5Breeze/WKnob/APP/BTHome/mbedtls/include/mbedtls/ssl.h

/**
 * \file ssl.h
 *
 * \brief SSL/TLS functions.
 */
/*
 *  Copyright The Mbed TLS Contributors
 *  SPDX-License-Identifier: Apache-2.0
 *
 *  Licensed under the Apache License, Version 2.0 (the "License"); you may
 *  not use this file except in compliance with the License.
 *  You may obtain a copy of the License at
 *
 *  http://www.apache.org/licenses/LICENSE-2.0
 *
 *  Unless required by applicable law or agreed to in writing, software
 *  distributed under the License is distributed on an "AS IS" BASIS, WITHOUT
 *  WARRANTIES OR CONDITIONS OF ANY KIND, either express or implied.
 *  See the License for the specific language governing permissions and
 *  limitations under the License.
 */
#ifndef MBEDTLS_SSL_H
#define MBEDTLS_SSL_H

#if !defined(MBEDTLS_CONFIG_FILE)
#include "config.h"
#else
#include MBEDTLS_CONFIG_FILE
#endif

#include "bignum.h"
#include "ecp.h"

#include "ssl_ciphersuites.h"

#if defined(MBEDTLS_X509_CRT_PARSE_C)
#include "x509_crt.h"
#include "x509_crl.h"
#endif

#if defined(MBEDTLS_DHM_C)
#include "dhm.h"
#endif

#if defined(MBEDTLS_ECDH_C)
#include "ecdh.h"
#endif

#if defined(MBEDTLS_ZLIB_SUPPORT)

#if defined(MBEDTLS_DEPRECATED_WARNING)
#warning "Record compression support via MBEDTLS_ZLIB_SUPPORT is deprecated and will be removed in the next major revision of the library"
#endif

#if defined(MBEDTLS_DEPRECATED_REMOVED)
#error "Record compression support via MBEDTLS_ZLIB_SUPPORT is deprecated and cannot be used if MBEDTLS_DEPRECATED_REMOVED is set"
#endif

#include "zlib.h"
#endif

#if defined(MBEDTLS_HAVE_TIME)
#include "platform_time.h"
#endif

#if defined(MBEDTLS_USE_PSA_CRYPTO)
#include "psa/crypto.h"
#endif /* MBEDTLS_USE_PSA_CRYPTO */

/*
 * SSL Error codes
 */
#define MBEDTLS_ERR_SSL_FEATURE_UNAVAILABLE               -0x7080  /**< The requested feature is not available. */
#define MBEDTLS_ERR_SSL_BAD_INPUT_DATA                    -0x7100  /**< Bad input parameters to function. */
#define MBEDTLS_ERR_SSL_INVALID_MAC                       -0x7180  /**< Verification of the message MAC failed. */
#define MBEDTLS_ERR_SSL_INVALID_RECORD                    -0x7200  /**< An invalid SSL record was received. */
#define MBEDTLS_ERR_SSL_CONN_EOF                          -0x7280  /**< The connection indicated an EOF. */
#define MBEDTLS_ERR_SSL_UNKNOWN_CIPHER                    -0x7300  /**< An unknown cipher was received. */
#define MBEDTLS_ERR_SSL_NO_CIPHER_CHOSEN                  -0x7380  /**< The server has no ciphersuites in common with the client. */
#define MBEDTLS_ERR_SSL_NO_RNG                            -0x7400  /**< No RNG was provided to the SSL module. */
#define MBEDTLS_ERR_SSL_NO_CLIENT_CERTIFICATE             -0x7480  /**< No client certification received from the client, but required by the authentication mode. */
#define MBEDTLS_ERR_SSL_CERTIFICATE_TOO_LARGE             -0x7500  /**< Our own certificate(s) is/are too large to send in an SSL message. */
#define MBEDTLS_ERR_SSL_CERTIFICATE_REQUIRED              -0x7580  /**< The own certificate is not set, but needed by the server. */
#define MBEDTLS_ERR_SSL_PRIVATE_KEY_REQUIRED              -0x7600  /**< The own private key or pre-shared key is not set, but needed. */
#define MBEDTLS_ERR_SSL_CA_CHAIN_REQUIRED                 -0x7680  /**< No CA Chain is set, but required to operate. */
#define MBEDTLS_ERR_SSL_UNEXPECTED_MESSAGE                -0x7700  /**< An unexpected message was received from our peer. */
#define MBEDTLS_ERR_SSL_FATAL_ALERT_MESSAGE               -0x7780  /**< A fatal alert message was received from our peer. */
#define MBEDTLS_ERR_SSL_PEER_VERIFY_FAILED                -0x7800  /**< Verification of our peer failed. */
#define MBEDTLS_ERR_SSL_PEER_CLOSE_NOTIFY                 -0x7880  /**< The peer notified us that the connection is going to be closed. */
#define MBEDTLS_ERR_SSL_BAD_HS_CLIENT_HELLO               -0x7900  /**< Processing of the ClientHello handshake message failed. */
#define MBEDTLS_ERR_SSL_BAD_HS_SERVER_HELLO               -0x7980  /**< Processing of the ServerHello handshake message failed. */
#define MBEDTLS_ERR_SSL_BAD_HS_CERTIFICATE                -0x7A00  /**< Processing of the Certificate handshake message failed. */
#define MBEDTLS_ERR_SSL_BAD_HS_CERTIFICATE_REQUEST        -0x7A80  /**< Processing of the CertificateRequest handshake message failed. */
#define MBEDTLS_ERR_SSL_BAD_HS_SERVER_KEY_EXCHANGE        -0x7B00  /**< Processing of the ServerKeyExchange handshake message failed. */
#define MBEDTLS_ERR_SSL_BAD_HS_SERVER_HELLO_DONE          -0x7B80  /**< Processing of the ServerHelloDone handshake message failed. */
#define MBEDTLS_ERR_SSL_BAD_HS_CLIENT_KEY_EXCHANGE        -0x7C00  /**< Processing of the ClientKeyExchange handshake message failed. */
#define MBEDTLS_ERR_SSL_BAD_HS_CLIENT_KEY_EXCHANGE_RP     -0x7C80  /**< Processing of the ClientKeyExchange handshake message failed in DHM / ECDH Read Public. */
#define MBEDTLS_ERR_SSL_BAD_HS_CLIENT_KEY_EXCHANGE_CS     -0x7D00  /**< Processing of the ClientKeyExchange handshake message failed in DHM / ECDH Calculate Secret. */
#define MBEDTLS_ERR_SSL_BAD_HS_CERTIFICATE_VERIFY         -0x7D80  /**< Processing of the CertificateVerify handshake message failed. */
#define MBEDTLS_ERR_SSL_BAD_HS_CHANGE_CIPHER_SPEC         -0x7E00  /**< Processing of the ChangeCipherSpec handshake message failed. */
#define MBEDTLS_ERR_SSL_BAD_HS_FINISHED                   -0x7E80  /**< Processing of the Finished handshake message failed. */
#define MBEDTLS_ERR_SSL_ALLOC_FAILED                      -0x7F00  /**< Memory allocation failed */
#define MBEDTLS_ERR_SSL_HW_ACCEL_FAILED                   -0x7F80  /**< Hardware acceleration function returned with error */
#define MBEDTLS_ERR_SSL_HW_ACCEL_FALLTHROUGH              -0x6F80  /**< Hardware acceleration function skipped / left alone data */
#define MBEDTLS_ERR_SSL_COMPRESSION_FAILED                -0x6F00  /**< Processing of the compression / decompression failed */
#define MBEDTLS_ERR_SSL_BAD_HS_PROTOCOL_VERSION           -0x6E80  /**< Handshake protocol not within min/max boundaries */
#define MBEDTLS_ERR_SSL_BAD_HS_NEW_SESSION_TICKET         -0x6E00  /**< Processing of the NewSessionTicket handshake message failed. */
#define MBEDTLS_ERR_SSL_SESSION_TICKET_EXPIRED            -0x6D80  /**< Session ticket has expired. */
#define MBEDTLS_ERR_SSL_PK_TYPE_MISMATCH                  -0x6D00  /**< Public key type mismatch (eg, asked for RSA key exchange and presented EC key) */
#define MBEDTLS_ERR_SSL_UNKNOWN_IDENTITY                  -0x6C80  /**< Unknown identity received (eg, PSK identity) */
#define MBEDTLS_ERR_SSL_INTERNAL_ERROR                    -0x6C00  /**< Internal error (eg, unexpected failure in lower-level module) */
#define MBEDTLS_ERR_SSL_COUNTER_WRAPPING                  -0x6B80  /**< A counter would wrap (eg, too many messages exchanged). */
#define MBEDTLS_ERR_SSL_WAITING_SERVER_HELLO_RENEGO       -0x6B00  /**< Unexpected message at ServerHello in renegotiation. */
#define MBEDTLS_ERR_SSL_HELLO_VERIFY_REQUIRED             -0x6A80  /**< DTLS client must retry for hello verification */
#define MBEDTLS_ERR_SSL_BUFFER_TOO_SMALL                  -0x6A00  /**< A buffer is too small to receive or write a message */
#define MBEDTLS_ERR_SSL_NO_USABLE_CIPHERSUITE             -0x6980  /**< None of the common ciphersuites is usable (eg, no suitable certificate, see debug messages). */
#define MBEDTLS_ERR_SSL_WANT_READ                         -0x6900  /**< No data of requested type currently available on underlying transport. */
#define MBEDTLS_ERR_SSL_WANT_WRITE                        -0x6880  /**< Connection requires a write call. */
#define MBEDTLS_ERR_SSL_TIMEOUT                           -0x6800  /**< The operation timed out. */
#define MBEDTLS_ERR_SSL_CLIENT_RECONNECT                  -0x6780  /**< The client initiated a reconnect from the same port. */
#define MBEDTLS_ERR_SSL_UNEXPECTED_RECORD                 -0x6700  /**< Record header looks valid but is not expected. */
#define MBEDTLS_ERR_SSL_NON_FATAL                         -0x6680  /**< The alert message received indicates a non-fatal error. */
#define MBEDTLS_ERR_SSL_INVALID_VERIFY_HASH               -0x6600  /**< Couldn't set the hash for verifying CertificateVerify */
#define MBEDTLS_ERR_SSL_CONTINUE_PROCESSING               -0x6580  /**< Internal-only message signaling that further message-processing should be done */
#define MBEDTLS_ERR_SSL_ASYNC_IN_PROGRESS                 -0x6500  /**< The asynchronous operation is not completed yet. */
#define MBEDTLS_ERR_SSL_EARLY_MESSAGE                     -0x6480  /**< Internal-only message signaling that a message arrived early. */
#define MBEDTLS_ERR_SSL_UNEXPECTED_CID                    -0x6000  /**< An encrypted DTLS-frame with an unexpected CID was received. */
#define MBEDTLS_ERR_SSL_VERSION_MISMATCH                  -0x5F00  /**< An operation failed due to an unexpected version or configuration. */
#define MBEDTLS_ERR_SSL_CRYPTO_IN_PROGRESS                -0x7000  /**< A cryptographic operation is in progress. Try again later. */
#define MBEDTLS_ERR_SSL_BAD_CONFIG                        -0x5E80  /**< Invalid value in SSL config */

/*
 * Various constants
 */
#define MBEDTLS_SSL_MAJOR_VERSION_3             3
#define MBEDTLS_SSL_MINOR_VERSION_0             0   /*!< SSL v3.0 */
#define MBEDTLS_SSL_MINOR_VERSION_1             1   /*!< TLS v1.0 */
#define MBEDTLS_SSL_MINOR_VERSION_2             2   /*!< TLS v1.1 */
#define MBEDTLS_SSL_MINOR_VERSION_3             3   /*!< TLS v1.2 */
#define MBEDTLS_SSL_MINOR_VERSION_4             4   /*!< TLS v1.3 (experimental) */

#define MBEDTLS_SSL_TRANSPORT_STREAM            0   /*!< TLS      */
#define MBEDTLS_SSL_TRANSPORT_DATAGRAM          1   /*!< DTLS     */

#define MBEDTLS_SSL_MAX_HOST_NAME_LEN           255 /*!< Maximum host name defined in RFC 1035 */
#define MBEDTLS_SSL_MAX_ALPN_NAME_LEN           255 /*!< Maximum size in bytes of a protocol name in alpn ext., RFC 7301 */

#define MBEDTLS_SSL_MAX_ALPN_LIST_LEN           65535 /*!< Maximum size in bytes of list in alpn ext., RFC 7301          */

/* RFC 6066 section 4, see also mfl_code_to_length in ssl_tls.c
 * NONE must be zero so that memset()ing structure to zero works */
#define MBEDTLS_SSL_MAX_FRAG_LEN_NONE           0   /*!< don't use this extension   */
#define MBEDTLS_SSL_MAX_FRAG_LEN_512            1   /*!< MaxFragmentLength 2^9      */
#define MBEDTLS_SSL_MAX_FRAG_LEN_1024           2   /*!< MaxFragmentLength 2^10     */
#define MBEDTLS_SSL_MAX_FRAG_LEN_2048           3   /*!< MaxFragmentLength 2^11     */
#define MBEDTLS_SSL_MAX_FRAG_LEN_4096           4   /*!< MaxFragmentLength 2^12     */
#define MBEDTLS_SSL_MAX_FRAG_LEN_INVALID        5   /*!< first invalid value        */

#define MBEDTLS_SSL_IS_CLIENT                   0
#define MBEDTLS_SSL_IS_SERVER                   1

#define MBEDTLS_SSL_IS_NOT_FALLBACK             0
#define MBEDTLS_SSL_IS_FALLBACK                 1

#define MBEDTLS_SSL_EXTENDED_MS_DISABLED        0
#define MBEDTLS_SSL_EXTENDED_MS_ENABLED         1

#define MBEDTLS_SSL_CID_DISABLED                0
#define MBEDTLS_SSL_CID_ENABLED                 1

#define MBEDTLS_SSL_ETM_DISABLED                0
#define MBEDTLS_SSL_ETM_ENABLED                 1

#define MBEDTLS_SSL_COMPRESS_NULL               0
#define MBEDTLS_SSL_COMPRESS_DEFLATE            1

#define MBEDTLS_SSL_VERIFY_NONE                 0
#define MBEDTLS_SSL_VERIFY_OPTIONAL             1
#define MBEDTLS_SSL_VERIFY_REQUIRED             2
#define MBEDTLS_SSL_VERIFY_UNSET                3 /* Used only for sni_authmode */

#define MBEDTLS_SSL_LEGACY_RENEGOTIATION        0
#define MBEDTLS_SSL_SECURE_RENEGOTIATION        1

#define MBEDTLS_SSL_RENEGOTIATION_DISABLED      0
#define MBEDTLS_SSL_RENEGOTIATION_ENABLED       1

#define MBEDTLS_SSL_ANTI_REPLAY_DISABLED        0
#define MBEDTLS_SSL_ANTI_REPLAY_ENABLED         1

#define MBEDTLS_SSL_RENEGOTIATION_NOT_ENFORCED  -1
#define MBEDTLS_SSL_RENEGO_MAX_RECORDS_DEFAULT  16

#define MBEDTLS_SSL_LEGACY_NO_RENEGOTIATION     0
#define MBEDTLS_SSL_LEGACY_ALLOW_RENEGOTIATION  1
#define MBEDTLS_SSL_LEGACY_BREAK_HANDSHAKE      2

#define MBEDTLS_SSL_TRUNC_HMAC_DISABLED         0
#define MBEDTLS_SSL_TRUNC_HMAC_ENABLED          1
#define MBEDTLS_SSL_TRUNCATED_HMAC_LEN          10  /* 80 bits, rfc 6066 section 7 */

#define MBEDTLS_SSL_SESSION_TICKETS_DISABLED     0
#define MBEDTLS_SSL_SESSION_TICKETS_ENABLED      1

#define MBEDTLS_SSL_CBC_RECORD_SPLITTING_DISABLED    0
#define MBEDTLS_SSL_CBC_RECORD_SPLITTING_ENABLED     1

#define MBEDTLS_SSL_ARC4_ENABLED                0
#define MBEDTLS_SSL_ARC4_DISABLED               1

#define MBEDTLS_SSL_PRESET_DEFAULT              0
#define MBEDTLS_SSL_PRESET_SUITEB               2

#define MBEDTLS_SSL_CERT_REQ_CA_LIST_ENABLED       1
#define MBEDTLS_SSL_CERT_REQ_CA_LIST_DISABLED      0

/*
 * Default range for DTLS retransmission timer value, in milliseconds.
 * RFC 6347 4.2.4.1 says from 1 second to 60 seconds.
 */
#define MBEDTLS_SSL_DTLS_TIMEOUT_DFL_MIN    1000
#define MBEDTLS_SSL_DTLS_TIMEOUT_DFL_MAX   60000

/**
 * \name SECTION: Module settings
 *
 * The configuration options you can set for this module are in this section.
 * Either change them in config.h or define them on the compiler command line.
 * \{
 */

#if !defined(MBEDTLS_SSL_DEFAULT_TICKET_LIFETIME)
#define MBEDTLS_SSL_DEFAULT_TICKET_LIFETIME     86400 /**< Lifetime of session tickets (if enabled) */
#endif

/*
 * Maximum fragment length in bytes,
 * determines the size of each of the two internal I/O buffers.
 *
 * Note: the RFC defines the default size of SSL / TLS messages. If you
 * change the value here, other clients / servers may not be able to
 * communicate with you anymore. Only change this value if you control
 * both sides of the connection and have it reduced at both sides, or
 * if you're using the Max Fragment Length extension and you know all your
 * peers are using it too!
 */
#if !defined(MBEDTLS_SSL_MAX_CONTENT_LEN)
#define MBEDTLS_SSL_MAX_CONTENT_LEN         16384   /**< Size of the input / output buffer */
#endif

#if !defined(MBEDTLS_SSL_IN_CONTENT_LEN)
#define MBEDTLS_SSL_IN_CONTENT_LEN MBEDTLS_SSL_MAX_CONTENT_LEN
#endif

#if !defined(MBEDTLS_SSL_OUT_CONTENT_LEN)
#define MBEDTLS_SSL_OUT_CONTENT_LEN MBEDTLS_SSL_MAX_CONTENT_LEN
#endif

/*
 * Maximum number of heap-allocated bytes for the purpose of
 * DTLS handshake message reassembly and future message buffering.
 */
#if !defined(MBEDTLS_SSL_DTLS_MAX_BUFFERING)
#define MBEDTLS_SSL_DTLS_MAX_BUFFERING 32768
#endif

/*
 * Maximum length of CIDs for incoming and outgoing messages.
 */
#if !defined(MBEDTLS_SSL_CID_IN_LEN_MAX)
#define MBEDTLS_SSL_CID_IN_LEN_MAX          32
#endif

#if !defined(MBEDTLS_SSL_CID_OUT_LEN_MAX)
#define MBEDTLS_SSL_CID_OUT_LEN_MAX         32
#endif

#if !defined(MBEDTLS_SSL_CID_PADDING_GRANULARITY)
#define MBEDTLS_SSL_CID_PADDING_GRANULARITY 16
#endif

#if !defined(MBEDTLS_SSL_TLS1_3_PADDING_GRANULARITY)
#define MBEDTLS_SSL_TLS1_3_PADDING_GRANULARITY 1
#endif

/* \} name SECTION: Module settings */

/*
 * Length of the verify data for secure renegotiation
 */
#if defined(MBEDTLS_SSL_PROTO_SSL3)
#define MBEDTLS_SSL_VERIFY_DATA_MAX_LEN 36
#else
#define MBEDTLS_SSL_VERIFY_DATA_MAX_LEN 12
#endif

/*
 * Signaling ciphersuite values (SCSV)
 */
#define MBEDTLS_SSL_EMPTY_RENEGOTIATION_INFO    0xFF   /**< renegotiation info ext */
#define MBEDTLS_SSL_FALLBACK_SCSV_VALUE         0x5600 /**< RFC 7507 section 2 */

/*
 * Supported Signature and Hash algorithms (For TLS 1.2)
 * RFC 5246 section 7.4.1.4.1
 */
#define MBEDTLS_SSL_HASH_NONE                0
#define MBEDTLS_SSL_HASH_MD5                 1
#define MBEDTLS_SSL_HASH_SHA1                2
#define MBEDTLS_SSL_HASH_SHA224              3
#define MBEDTLS_SSL_HASH_SHA256              4
#define MBEDTLS_SSL_HASH_SHA384              5
#define MBEDTLS_SSL_HASH_SHA512              6

#define MBEDTLS_SSL_SIG_ANON                 0
#define MBEDTLS_SSL_SIG_RSA                  1
#define MBEDTLS_SSL_SIG_ECDSA                3

/*
 * Client Certificate Types
 * RFC 5246 section 7.4.4 plus RFC 4492 section 5.5
 */
#define MBEDTLS_SSL_CERT_TYPE_RSA_SIGN       1
#define MBEDTLS_SSL_CERT_TYPE_ECDSA_SIGN    64

/*
 * Message, alert and handshake types
 */
#define MBEDTLS_SSL_MSG_CHANGE_CIPHER_SPEC     20
#define MBEDTLS_SSL_MSG_ALERT                  21
#define MBEDTLS_SSL_MSG_HANDSHAKE              22
#define MBEDTLS_SSL_MSG_APPLICATION_DATA       23
#define MBEDTLS_SSL_MSG_CID                    25

#define MBEDTLS_SSL_ALERT_LEVEL_WARNING         1
#define MBEDTLS_SSL_ALERT_LEVEL_FATAL           2

#define MBEDTLS_SSL_ALERT_MSG_CLOSE_NOTIFY           0  /* 0x00 */
#define MBEDTLS_SSL_ALERT_MSG_UNEXPECTED_MESSAGE    10  /* 0x0A */
#define MBEDTLS_SSL_ALERT_MSG_BAD_RECORD_MAC        20  /* 0x14 */
#define MBEDTLS_SSL_ALERT_MSG_DECRYPTION_FAILED     21  /* 0x15 */
#define MBEDTLS_SSL_ALERT_MSG_RECORD_OVERFLOW       22  /* 0x16 */
#define MBEDTLS_SSL_ALERT_MSG_DECOMPRESSION_FAILURE 30  /* 0x1E */
#define MBEDTLS_SSL_ALERT_MSG_HANDSHAKE_FAILURE     40  /* 0x28 */
#define MBEDTLS_SSL_ALERT_MSG_NO_CERT               41  /* 0x29 */
#define MBEDTLS_SSL_ALERT_MSG_BAD_CERT              42  /* 0x2A */
#define MBEDTLS_SSL_ALERT_MSG_UNSUPPORTED_CERT      43  /* 0x2B */
#define MBEDTLS_SSL_ALERT_MSG_CERT_REVOKED          44  /* 0x2C */
#define MBEDTLS_SSL_ALERT_MSG_CERT_EXPIRED          45  /* 0x2D */
#define MBEDTLS_SSL_ALERT_MSG_CERT_UNKNOWN          46  /* 0x2E */
#define MBEDTLS_SSL_ALERT_MSG_ILLEGAL_PARAMETER     47  /* 0x2F */
#define MBEDTLS_SSL_ALERT_MSG_UNKNOWN_CA            48  /* 0x30 */
#define MBEDTLS_SSL_ALERT_MSG_ACCESS_DENIED         49  /* 0x31 */
#define MBEDTLS_SSL_ALERT_MSG_DECODE_ERROR          50  /* 0x32 */
#define MBEDTLS_SSL_ALERT_MSG_DECRYPT_ERROR         51  /* 0x33 */
#define MBEDTLS_SSL_ALERT_MSG_EXPORT_RESTRICTION    60  /* 0x3C */
#define MBEDTLS_SSL_ALERT_MSG_PROTOCOL_VERSION      70  /* 0x46 */
#define MBEDTLS_SSL_ALERT_MSG_INSUFFICIENT_SECURITY 71  /* 0x47 */
#define MBEDTLS_SSL_ALERT_MSG_INTERNAL_ERROR        80  /* 0x50 */
#define MBEDTLS_SSL_ALERT_MSG_INAPROPRIATE_FALLBACK 86  /* 0x56 */
#define MBEDTLS_SSL_ALERT_MSG_USER_CANCELED         90  /* 0x5A */
#define MBEDTLS_SSL_ALERT_MSG_NO_RENEGOTIATION     100  /* 0x64 */
#define MBEDTLS_SSL_ALERT_MSG_UNSUPPORTED_EXT      110  /* 0x6E */
#define MBEDTLS_SSL_ALERT_MSG_UNRECOGNIZED_NAME    112  /* 0x70 */
#define MBEDTLS_SSL_ALERT_MSG_UNKNOWN_PSK_IDENTITY 115  /* 0x73 */
#define MBEDTLS_SSL_ALERT_MSG_NO_APPLICATION_PROTOCOL 120 /* 0x78 */

#define MBEDTLS_SSL_HS_HELLO_REQUEST            0
#define MBEDTLS_SSL_HS_CLIENT_HELLO             1
#define MBEDTLS_SSL_HS_SERVER_HELLO             2
#define MBEDTLS_SSL_HS_HELLO_VERIFY_REQUEST     3
#define MBEDTLS_SSL_HS_NEW_SESSION_TICKET       4
#define MBEDTLS_SSL_HS_CERTIFICATE             11
#define MBEDTLS_SSL_HS_SERVER_KEY_EXCHANGE     12
#define MBEDTLS_SSL_HS_CERTIFICATE_REQUEST     13
#define MBEDTLS_SSL_HS_SERVER_HELLO_DONE       14
#define MBEDTLS_SSL_HS_CERTIFICATE_VERIFY      15
#define MBEDTLS_SSL_HS_CLIENT_KEY_EXCHANGE     16
#define MBEDTLS_SSL_HS_FINISHED                20

/*
 * TLS extensions
 */
#define MBEDTLS_TLS_EXT_SERVERNAME                   0
#define MBEDTLS_TLS_EXT_SERVERNAME_HOSTNAME          0

#define MBEDTLS_TLS_EXT_MAX_FRAGMENT_LENGTH          1

#define MBEDTLS_TLS_EXT_TRUNCATED_HMAC               4

#define MBEDTLS_TLS_EXT_SUPPORTED_ELLIPTIC_CURVES   10
#define MBEDTLS_TLS_EXT_SUPPORTED_POINT_FORMATS     11

#define MBEDTLS_TLS_EXT_SIG_ALG                     13

#define MBEDTLS_TLS_EXT_ALPN                        16

#define MBEDTLS_TLS_EXT_ENCRYPT_THEN_MAC            22 /* 0x16 */
#define MBEDTLS_TLS_EXT_EXTENDED_MASTER_SECRET  0x0017 /* 23 */

#define MBEDTLS_TLS_EXT_SESSION_TICKET              35

/* The value of the CID extension is still TBD as of
 * draft-ietf-tls-dtls-connection-id-05
 * (https://tools.ietf.org/html/draft-ietf-tls-dtls-connection-id-05) */
#define MBEDTLS_TLS_EXT_CID                        254 /* TBD */

#define MBEDTLS_TLS_EXT_ECJPAKE_KKPP               256 /* experimental */

#define MBEDTLS_TLS_EXT_RENEGOTIATION_INFO      0xFF01

/*
 * Size defines
 */
#if !defined(MBEDTLS_PSK_MAX_LEN)
#define MBEDTLS_PSK_MAX_LEN            32 /* 256 bits */
#endif

/* Dummy type used only for its size */
union mbedtls_ssl_premaster_secret
{
#if defined(MBEDTLS_KEY_EXCHANGE_RSA_ENABLED)
    unsigned char _pms_rsa[48];                         /* RFC 5246 8.1.1 */
#endif
#if defined(MBEDTLS_KEY_EXCHANGE_DHE_RSA_ENABLED)
    unsigned char _pms_dhm[MBEDTLS_MPI_MAX_SIZE];      /* RFC 5246 8.1.2 */
#endif
#if defined(MBEDTLS_KEY_EXCHANGE_ECDHE_RSA_ENABLED)    || \
    defined(MBEDTLS_KEY_EXCHANGE_ECDHE_ECDSA_ENABLED)  || \
    defined(MBEDTLS_KEY_EXCHANGE_ECDH_RSA_ENABLED)     || \
    defined(MBEDTLS_KEY_EXCHANGE_ECDH_ECDSA_ENABLED)
    unsigned char _pms_ecdh[MBEDTLS_ECP_MAX_BYTES];    /* RFC 4492 5.10 */
#endif
#if defined(MBEDTLS_KEY_EXCHANGE_PSK_ENABLED)
    unsigned char _pms_psk[4 + 2 * MBEDTLS_PSK_MAX_LEN];       /* RFC 4279 2 */
#endif
#if defined(MBEDTLS_KEY_EXCHANGE_DHE_PSK_ENABLED)
    unsigned char _pms_dhe_psk[4 + MBEDTLS_MPI_MAX_SIZE
                                 + MBEDTLS_PSK_MAX_LEN];       /* RFC 4279 3 */
#endif
#if defined(MBEDTLS_KEY_EXCHANGE_RSA_PSK_ENABLED)
    unsigned char _pms_rsa_psk[52 + MBEDTLS_PSK_MAX_LEN];      /* RFC 4279 4 */
#endif
#if defined(MBEDTLS_KEY_EXCHANGE_ECDHE_PSK_ENABLED)
    unsigned char _pms_ecdhe_psk[4 + MBEDTLS_ECP_MAX_BYTES
                                   + MBEDTLS_PSK_MAX_LEN];     /* RFC 5489 2 */
#endif
#if defined(MBEDTLS_KEY_EXCHANGE_ECJPAKE_ENABLED)
    unsigned char _pms_ecjpake[32];     /* Thread spec: SHA-256 output */
#endif
};

#define MBEDTLS_PREMASTER_SIZE     sizeof( union mbedtls_ssl_premaster_secret )

#ifdef __cplusplus
extern "C" {
#endif

/*
 * SSL state machine
 */
typedef enum
{
    MBEDTLS_SSL_HELLO_REQUEST,
    MBEDTLS_SSL_CLIENT_HELLO,
    MBEDTLS_SSL_SERVER_HELLO,
    MBEDTLS_SSL_SERVER_CERTIFICATE,
    MBEDTLS_SSL_SERVER_KEY_EXCHANGE,
    MBEDTLS_SSL_CERTIFICATE_REQUEST,
    MBEDTLS_SSL_SERVER_HELLO_DONE,
    MBEDTLS_SSL_CLIENT_CERTIFICATE,
    MBEDTLS_SSL_CLIENT_KEY_EXCHANGE,
    MBEDTLS_SSL_CERTIFICATE_VERIFY,
    MBEDTLS_SSL_CLIENT_CHANGE_CIPHER_SPEC,
    MBEDTLS_SSL_CLIENT_FINISHED,
    MBEDTLS_SSL_SERVER_CHANGE_CIPHER_SPEC,
    MBEDTLS_SSL_SERVER_FINISHED,
    MBEDTLS_SSL_FLUSH_BUFFERS,
    MBEDTLS_SSL_HANDSHAKE_WRAPUP,
    MBEDTLS_SSL_HANDSHAKE_OVER,
    MBEDTLS_SSL_SERVER_NEW_SESSION_TICKET,
    MBEDTLS_SSL_SERVER_HELLO_VERIFY_REQUEST_SENT,
}
mbedtls_ssl_states;

/*
 * The tls_prf function types.
 */
typedef enum
{
   MBEDTLS_SSL_TLS_PRF_NONE,
   MBEDTLS_SSL_TLS_PRF_SSL3,
   MBEDTLS_SSL_TLS_PRF_TLS1,
   MBEDTLS_SSL_TLS_PRF_SHA384,
   MBEDTLS_SSL_TLS_PRF_SHA256
}
mbedtls_tls_prf_types;
/**
 * \brief          Callback type: send data on the network.
 *
 * \note           That callback may be either blocking or non-blocking.
 *
 * \param ctx      Context for the send callback (typically a file descriptor)
 * \param buf      Buffer holding the data to send
 * \param len      Length of the data to send
 *
 * \return         The callback must return the number of bytes sent if any,
 *                 or a non-zero error code.
 *                 If performing non-blocking I/O, \c MBEDTLS_ERR_SSL_WANT_WRITE
 *                 must be returned when the operation would block.
 *
 * \note           The callback is allowed to send fewer bytes than requested.
 *                 It must always return the number of bytes actually sent.
 */
typedef int mbedtls_ssl_send_t( void *ctx,
                                const unsigned char *buf,
                                size_t len );

/**
 * \brief          Callback type: receive data from the network.
 *
 * \note           That callback may be either blocking or non-blocking.
 *
 * \param ctx      Context for the receive callback (typically a file
 *                 descriptor)
 * \param buf      Buffer to write the received data to
 * \param len      Length of the receive buffer
 *
 * \return         The callback must return the number of bytes received,
 *                 or a non-zero error code.
 *                 If performing non-blocking I/O, \c MBEDTLS_ERR_SSL_WANT_READ
 *                 must be returned when the operation would block.
 *
 * \note           The callback may receive fewer bytes than the length of the
 *                 buffer. It must always return the number of bytes actually
 *                 received and written to the buffer.
 */
typedef int mbedtls_ssl_recv_t( void *ctx,
                                unsigned char *buf,
                                size_t len );

/**
 * \brief          Callback type: receive data from the network, with timeout
 *
 * \note           That callback must block until data is received, or the
 *                 timeout delay expires, or the operation is interrupted by a
 *                 signal.
 *
 * \param ctx      Context for the receive callback (typically a file descriptor)
 * \param buf      Buffer to write the received data to
 * \param len      Length of the receive buffer
 * \param timeout  Maximum nomber of millisecondes to wait for data
 *                 0 means no timeout (potentially waiting forever)
 *
 * \return         The callback must return the number of bytes received,
 *                 or a non-zero error code:
 *                 \c MBEDTLS_ERR_SSL_TIMEOUT if the operation timed out,
 *                 \c MBEDTLS_ERR_SSL_WANT_READ if interrupted by a signal.
 *
 * \note           The callback may receive fewer bytes than the length of the
 *                 buffer. It must always return the number of bytes actually
 *                 received and written to the buffer.
 */
typedef int mbedtls_ssl_recv_timeout_t( void *ctx,
                                        unsigned char *buf,
                                        size_t len,
                                        uint32_t timeout );
/**
 * \brief          Callback type: set a pair of timers/delays to watch
 *
 * \param ctx      Context pointer
 * \param int_ms   Intermediate delay in milliseconds
 * \param fin_ms   Final delay in milliseconds
 *                 0 cancels the current timer.
 *
 * \note           This callback must at least store the necessary information
 *                 for the associated \c mbedtls_ssl_get_timer_t callback to
 *                 return correct information.
 *
 * \note           If using a event-driven style of programming, an event must
 *                 be generated when the final delay is passed. The event must
 *                 cause a call to \c mbedtls_ssl_handshake() with the proper
 *                 SSL context to be scheduled. Care must be taken to ensure
 *                 that at most one such call happens at a time.
 *
 * \note           Only one timer at a time must be running. Calling this
 *                 function while a timer is running must cancel it. Cancelled
 *                 timers must not generate any event.
 */
typedef void mbedtls_ssl_set_timer_t( void * ctx,
                                      uint32_t int_ms,
                                      uint32_t fin_ms );

/**
 * \brief          Callback type: get status of timers/delays
 *
 * \param ctx      Context pointer
 *
 * \return         This callback must return:
 *                 -1 if cancelled (fin_ms == 0),
 *                  0 if none of the delays have passed,
 *                  1 if only the intermediate delay has passed,
 *                  2 if the final delay has passed.
 */
typedef int mbedtls_ssl_get_timer_t( void * ctx );

/* Defined below */
typedef struct mbedtls_ssl_session mbedtls_ssl_session;
typedef struct mbedtls_ssl_context mbedtls_ssl_context;
typedef struct mbedtls_ssl_config  mbedtls_ssl_config;

/* Defined in ssl_internal.h */
typedef struct mbedtls_ssl_transform mbedtls_ssl_transform;
typedef struct mbedtls_ssl_handshake_params mbedtls_ssl_handshake_params;
typedef struct mbedtls_ssl_sig_hash_set_t mbedtls_ssl_sig_hash_set_t;
#if defined(MBEDTLS_X509_CRT_PARSE_C)
typedef struct mbedtls_ssl_key_cert mbedtls_ssl_key_cert;
#endif
#if defined(MBEDTLS_SSL_PROTO_DTLS)
typedef struct mbedtls_ssl_flight_item mbedtls_ssl_flight_item;
#endif

#if defined(MBEDTLS_SSL_ASYNC_PRIVATE)
#if defined(MBEDTLS_X509_CRT_PARSE_C)
/**
 * \brief           Callback type: start external signature operation.
 *
 *                  This callback is called during an SSL handshake to start
 *                  a signature decryption operation using an
 *                  external processor. The parameter \p cert contains
 *                  the public key; it is up to the callback function to
 *                  determine how to access the associated private key.
 *
 *                  This function typically sends or enqueues a request, and
 *                  does not wait for the operation to complete. This allows
 *                  the handshake step to be non-blocking.
 *
 *                  The parameters \p ssl and \p cert are guaranteed to remain
 *                  valid throughout the handshake. On the other hand, this
 *                  function must save the contents of \p hash if the value
 *                  is needed for later processing, because the \p hash buffer
 *                  is no longer valid after this function returns.
 *
 *                  This function may call mbedtls_ssl_set_async_operation_data()
 *                  to store an operation context for later retrieval
 *                  by the resume or cancel callback.
 *
 * \note            For RSA signatures, this function must produce output
 *                  that is consistent with PKCS#1 v1.5 in the same way as
 *                  mbedtls_rsa_pkcs1_sign(). Before the private key operation,
 *                  apply the padding steps described in RFC 8017, section 9.2
 *                  "EMSA-PKCS1-v1_5" as follows.
 *                  - If \p md_alg is #MBEDTLS_MD_NONE, apply the PKCS#1 v1.5
 *                    encoding, treating \p hash as the DigestInfo to be
 *                    padded. In other words, apply EMSA-PKCS1-v1_5 starting
 *                    from step 3, with `T = hash` and `tLen = hash_len`.
 *                  - If `md_alg != MBEDTLS_MD_NONE`, apply the PKCS#1 v1.5
 *                    encoding, treating \p hash as the hash to be encoded and
 *                    padded. In other words, apply EMSA-PKCS1-v1_5 starting
 *                    from step 2, with `digestAlgorithm` obtained by calling
 *                    mbedtls_oid_get_oid_by_md() on \p md_alg.
 *
 * \note            For ECDSA signatures, the output format is the DER encoding
 *                  `Ecdsa-Sig-Value` defined in
 *                  [RFC 4492 section 5.4](https://tools.ietf.org/html/rfc4492#section-5.4).
 *
 * \param ssl             The SSL connection instance. It should not be
 *                        modified other than via
 *                        mbedtls_ssl_set_async_operation_data().
 * \param cert            Certificate containing the public key.
 *                        In simple cases, this is one of the pointers passed to
 *                        mbedtls_ssl_conf_own_cert() when configuring the SSL
 *                        connection. However, if other callbacks are used, this
 *                        property may not hold. For example, if an SNI callback
 *                        is registered with mbedtls_ssl_conf_sni(), then
 *                        this callback determines what certificate is used.
 * \param md_alg          Hash algorithm.
 * \param hash            Buffer containing the hash. This buffer is
 *                        no longer valid when the function returns.
 * \param hash_len        Size of the \c hash buffer in bytes.
 *
 * \return          0 if the operation was started successfully and the SSL
 *                  stack should call the resume callback immediately.
 * \return          #MBEDTLS_ERR_SSL_ASYNC_IN_PROGRESS if the operation
 *                  was started successfully and the SSL stack should return
 *                  immediately without calling the resume callback yet.
 * \return          #MBEDTLS_ERR_SSL_HW_ACCEL_FALLTHROUGH if the external
 *                  processor does not support this key. The SSL stack will
 *                  use the private key object instead.
 * \return          Any other error indicates a fatal failure and is
 *                  propagated up the call chain. The callback should
 *                  use \c MBEDTLS_ERR_PK_xxx error codes, and <b>must not</b>
 *                  use \c MBEDTLS_ERR_SSL_xxx error codes except as
 *                  directed in the documentation of this callback.
 */
typedef int mbedtls_ssl_async_sign_t( mbedtls_ssl_context *ssl,
                                      mbedtls_x509_crt *cert,
                                      mbedtls_md_type_t md_alg,
                                      const unsigned char *hash,
                                      size_t hash_len );

/**
 * \brief           Callback type: start external decryption operation.
 *
 *                  This callback is called during an SSL handshake to start
 *                  an RSA decryption operation using an
 *                  external processor. The parameter \p cert contains
 *                  the public key; it is up to the callback function to
 *                  determine how to access the associated private key.
 *
 *                  This function typically sends or enqueues a request, and
 *                  does not wait for the operation to complete. This allows
 *                  the handshake step to be non-blocking.
 *
 *                  The parameters \p ssl and \p cert are guaranteed to remain
 *                  valid throughout the handshake. On the other hand, this
 *                  function must save the contents of \p input if the value
 *                  is needed for later processing, because the \p input buffer
 *                  is no longer valid after this function returns.
 *
 *                  This function may call mbedtls_ssl_set_async_operation_data()
 *                  to store an operation context for later retrieval
 *                  by the resume or cancel callback.
 *
 * \warning         RSA decryption as used in TLS is subject to a potential
 *                  timing side channel attack first discovered by Bleichenbacher
 *                  in 1998. This attack can be remotely exploitable
 *                  in practice. To avoid this attack, you must ensure that
 *                  if the callback performs an RSA decryption, the time it
 *                  takes to execute and return the result does not depend
 *                  on whether the RSA decryption succeeded or reported
 *                  invalid padding.
 *
 * \param ssl             The SSL connection instance. It should not be
 *                        modified other than via
 *                        mbedtls_ssl_set_async_operation_data().
 * \param cert            Certificate containing the public key.
 *                        In simple cases, this is one of the pointers passed to
 *                        mbedtls_ssl_conf_own_cert() when configuring the SSL
 *                        connection. However, if other callbacks are used, this
 *                        property may not hold. For example, if an SNI callback
 *                        is registered with mbedtls_ssl_conf_sni(), then
 *                        this callback determines what certificate is used.
 * \param input           Buffer containing the input ciphertext. This buffer
 *                        is no longer valid when the function returns.
 * \param input_len       Size of the \p input buffer in bytes.
 *
 * \return          0 if the operation was started successfully and the SSL
 *                  stack should call the resume callback immediately.
 * \return          #MBEDTLS_ERR_SSL_ASYNC_IN_PROGRESS if the operation
 *                  was started successfully and the SSL stack should return
 *                  immediately without calling the resume callback yet.
 * \return          #MBEDTLS_ERR_SSL_HW_ACCEL_FALLTHROUGH if the external
 *                  processor does not support this key. The SSL stack will
 *                  use the private key object instead.
 * \return          Any other error indicates a fatal failure and is
 *                  propagated up the call chain. The callback should
 *                  use \c MBEDTLS_ERR_PK_xxx error codes, and <b>must not</b>
 *                  use \c MBEDTLS_ERR_SSL_xxx error codes except as
 *                  directed in the documentation of this callback.
 */
typedef int mbedtls_ssl_async_decrypt_t( mbedtls_ssl_context *ssl,
                                         mbedtls_x509_crt *cert,
                                         const unsigned char *input,
                                         size_t input_len );
#endif /* MBEDTLS_X509_CRT_PARSE_C */

/**
 * \brief           Callback type: resume external operation.
 *
 *                  This callback is called during an SSL handshake to resume
 *                  an external operation started by the
 *                  ::mbedtls_ssl_async_sign_t or
 *                  ::mbedtls_ssl_async_decrypt_t callback.
 *
 *                  This function typically checks the status of a pending
 *                  request or causes the request queue to make progress, and
 *                  does not wait for the operation to complete. This allows
 *                  the handshake step to be non-blocking.
 *
 *                  This function may call mbedtls_ssl_get_async_operation_data()
 *                  to retrieve an operation context set by the start callback.
 *                  It may call mbedtls_ssl_set_async_operation_data() to modify
 *                  this context.
 *
 *                  Note that when this function returns a status other than
 *                  #MBEDTLS_ERR_SSL_ASYNC_IN_PROGRESS, it must free any
 *                  resources associated with the operation.
 *
 * \param ssl             The SSL connection instance. It should not be
 *                        modified other than via
 *                        mbedtls_ssl_set_async_operation_data().
 * \param output          Buffer containing the output (signature or decrypted
 *                        data) on success.
 * \param output_len      On success, number of bytes written to \p output.
 * \param output_size     Size of the \p output buffer in bytes.
 *
 * \return          0 if output of the operation is available in the
 *                  \p output buffer.
 * \return          #MBEDTLS_ERR_SSL_ASYNC_IN_PROGRESS if the operation
 *                  is still in progress. Subsequent requests for progress
 *                  on the SSL connection will call the resume callback
 *                  again.
 * \return          Any other error means that the operation is aborted.
 *                  The SSL handshake is aborted. The callback should
 *                  use \c MBEDTLS_ERR_PK_xxx error codes, and <b>must not</b>
 *                  use \c MBEDTLS_ERR_SSL_xxx error codes except as
 *                  directed in the documentation of this callback.
 */
typedef int mbedtls_ssl_async_resume_t( mbedtls_ssl_context *ssl,
                                        unsigned char *output,
                                        size_t *output_len,
                                        size_t output_size );

/**
 * \brief           Callback type: cancel external operation.
 *
 *                  This callback is called if an SSL connection is closed
 *                  while an asynchronous operation is in progress. Note that
 *                  this callback is not called if the
 *                  ::mbedtls_ssl_async_resume_t callback has run and has
 *                  returned a value other than
 *                  #MBEDTLS_ERR_SSL_ASYNC_IN_PROGRESS, since in that case
 *                  the asynchronous operation has already completed.
 *
 *                  This function may call mbedtls_ssl_get_async_operation_data()
 *                  to retrieve an operation context set by the start callback.
 *
 * \param ssl             The SSL connection instance. It should not be
 *                        modified.
 */
typedef void mbedtls_ssl_async_cancel_t( mbedtls_ssl_context *ssl );
#endif /* MBEDTLS_SSL_ASYNC_PRIVATE */

#if defined(MBEDTLS_KEY_EXCHANGE_WITH_CERT_ENABLED) &&        \
    !defined(MBEDTLS_SSL_KEEP_PEER_CERTIFICATE)
#define MBEDTLS_SSL_PEER_CERT_DIGEST_MAX_LEN  48
#if defined(MBEDTLS_SHA256_C)
#define MBEDTLS_SSL_PEER_CERT_DIGEST_DFL_TYPE MBEDTLS_MD_SHA256
#define MBEDTLS_SSL_PEER_CERT_DIGEST_DFL_LEN  32
#elif defined(MBEDTLS_SHA512_C)
#define MBEDTLS_SSL_PEER_CERT_DIGEST_DFL_TYPE MBEDTLS_MD_SHA384
#define MBEDTLS_SSL_PEER_CERT_DIGEST_DFL_LEN  48
#elif defined(MBEDTLS_SHA1_C)
#define MBEDTLS_SSL_PEER_CERT_DIGEST_DFL_TYPE MBEDTLS_MD_SHA1
#define MBEDTLS_SSL_PEER_CERT_DIGEST_DFL_LEN  20
#else
/* This is already checked in check_config.h, but be sure. */
#error "Bad configuration - need SHA-1, SHA-256 or SHA-512 enabled to compute digest of peer CRT."
#endif
#endif /* MBEDTLS_KEY_EXCHANGE_WITH_CERT_ENABLED &&
          !MBEDTLS_SSL_KEEP_PEER_CERTIFICATE */

/*
 * This structure is used for storing current session data.
 *
 * Note: when changing this definition, we need to check and update:
 *  - in tests/suites/test_suite_ssl.function:
 *      ssl_populate_session() and ssl_serialize_session_save_load()
 *  - in library/ssl_tls.c:
 *      mbedtls_ssl_session_init() and mbedtls_ssl_session_free()
 *      mbedtls_ssl_session_save() and ssl_session_load()
 *      ssl_session_copy()
 */
struct mbedtls_ssl_session
{
#if defined(MBEDTLS_HAVE_TIME)
    mbedtls_time_t start;       /*!< starting time      */
#endif
    int ciphersuite;            /*!< chosen ciphersuite */
    int compression;            /*!< chosen compression */
    size_t id_len;              /*!< session id length  */
    unsigned char id[32];       /*!< session identifier */
    unsigned char master[48];   /*!< the master secret  */

#if defined(MBEDTLS_X509_CRT_PARSE_C)
#if defined(MBEDTLS_SSL_KEEP_PEER_CERTIFICATE)
    mbedtls_x509_crt *peer_cert;       /*!< peer X.509 cert chain */
#else /* MBEDTLS_SSL_KEEP_PEER_CERTIFICATE */
    /*! The digest of the peer's end-CRT. This must be kept to detect CRT
     *  changes during renegotiation, mitigating the triple handshake attack. */
    unsigned char *peer_cert_digest;
    size_t peer_cert_digest_len;
    mbedtls_md_type_t peer_cert_digest_type;
#endif /* !MBEDTLS_SSL_KEEP_PEER_CERTIFICATE */
#endif /* MBEDTLS_X509_CRT_PARSE_C */
    uint32_t verify_result;          /*!<  verification result     */

#if defined(MBEDTLS_SSL_SESSION_TICKETS) && defined(MBEDTLS_SSL_CLI_C)
    unsigned char *ticket;      /*!< RFC 5077 session ticket */
    size_t ticket_len;          /*!< session ticket length   */
    uint32_t ticket_lifetime;   /*!< ticket lifetime hint    */
#endif /* MBEDTLS_SSL_SESSION_TICKETS && MBEDTLS_SSL_CLI_C */

#if defined(MBEDTLS_SSL_MAX_FRAGMENT_LENGTH)
    unsigned char mfl_code;     /*!< MaxFragmentLength negotiated by peer */
#endif /* MBEDTLS_SSL_MAX_FRAGMENT_LENGTH */

#if defined(MBEDTLS_SSL_TRUNCATED_HMAC)
    int trunc_hmac;             /*!< flag for truncated hmac activation   */
#endif /* MBEDTLS_SSL_TRUNCATED_HMAC */

#if defined(MBEDTLS_SSL_ENCRYPT_THEN_MAC)
    int encrypt_then_mac;       /*!< flag for EtM activation                */
#endif
};

/**
 * SSL/TLS configuration to be shared between mbedtls_ssl_context structures.
 */
struct mbedtls_ssl_config
{
    /* Group items by size (largest first) to minimize padding overhead */

    /*
     * Pointers
     */

    const int *ciphersuite_list[4]; /*!< allowed ciphersuites per version   */

    /** Callback for printing debug output                                  */
    void (*f_dbg)(void *, int, const char *, int, const char *);
    void *p_dbg;                    /*!< context for the debug function     */

    /** Callback for getting (pseudo-)random numbers                        */
    int  (*f_rng)(void *, unsigned char *, size_t);
    void *p_rng;                    /*!< context for the RNG function       */

    /** Callback to retrieve a session from the cache                       */
    int (*f_get_cache)(void *, mbedtls_ssl_session *);
    /** Callback to store a session into the cache                          */
    int (*f_set_cache)(void *, const mbedtls_ssl_session *);
    void *p_cache;                  /*!< context for cache callbacks        */

#if defined(MBEDTLS_SSL_SERVER_NAME_INDICATION)
    /** Callback for setting cert according to SNI extension                */
    int (*f_sni)(void *, mbedtls_ssl_context *, const unsigned char *, size_t);
    void *p_sni;                    /*!< context for SNI callback           */
#endif

#if defined(MBEDTLS_X509_CRT_PARSE_C)
    /** Callback to customize X.509 certificate chain verification          */
    int (*f_vrfy)(void *, mbedtls_x509_crt *, int, uint32_t *);
    void *p_vrfy;                   /*!< context for X.509 verify calllback */
#endif

#if defined(MBEDTLS_KEY_EXCHANGE_SOME_PSK_ENABLED)
    /** Callback to retrieve PSK key from identity                          */
    int (*f_psk)(void *, mbedtls_ssl_context *, const unsigned char *, size_t);
    void *p_psk;                    /*!< context for PSK callback           */
#endif

#if defined(MBEDTLS_SSL_DTLS_HELLO_VERIFY) && defined(MBEDTLS_SSL_SRV_C)
    /** Callback to create & write a cookie for ClientHello veirifcation    */
    int (*f_cookie_write)( void *, unsigned char **, unsigned char *,
                           const unsigned char *, size_t );
    /** Callback to verify validity of a ClientHello cookie                 */
    int (*f_cookie_check)( void *, const unsigned char *, size_t,
                           const unsigned char *, size_t );
    void *p_cookie;                 /*!< context for the cookie callbacks   */
#endif

#if defined(MBEDTLS_SSL_SESSION_TICKETS) && defined(MBEDTLS_SSL_SRV_C)
    /** Callback to create & write a session ticket                         */
    int (*f_ticket_write)( void *, const mbedtls_ssl_session *,
            unsigned char *, const unsigned char *, size_t *, uint32_t * );
    /** Callback to parse a session ticket into a session structure         */
    int (*f_ticket_parse)( void *, mbedtls_ssl_session *, unsigned char *, size_t);
    void *p_ticket;                 /*!< context for the ticket callbacks   */
#endif /* MBEDTLS_SSL_SESSION_TICKETS && MBEDTLS_SSL_SRV_C */

#if defined(MBEDTLS_SSL_EXPORT_KEYS)
    /** Callback to export key block and master secret                      */
    int (*f_export_keys)( void *, const unsigned char *,
            const unsigned char *, size_t, size_t, size_t );
    /** Callback to export key block, master secret,
     *  tls_prf and random bytes. Should replace f_export_keys    */
    int (*f_export_keys_ext)( void *, const unsigned char *,
                const unsigned char *, size_t, size_t, size_t,
                const unsigned char[32], const unsigned char[32],
                mbedtls_tls_prf_types );
    void *p_export_keys;            /*!< context for key export callback    */
#endif

#if defined(MBEDTLS_SSL_DTLS_CONNECTION_ID)
    size_t cid_len; /*!< The length of CIDs for incoming DTLS records.      */
#endif /* MBEDTLS_SSL_DTLS_CONNECTION_ID */

#if defined(MBEDTLS_X509_CRT_PARSE_C)
    const mbedtls_x509_crt_profile *cert_profile; /*!< verification profile */
    mbedtls_ssl_key_cert *key_cert; /*!< own certificate/key pair(s)        */
    mbedtls_x509_crt *ca_chain;     /*!< trusted CAs                        */
    mbedtls_x509_crl *ca_crl;       /*!< trusted CAs CRLs                   */
#if defined(MBEDTLS_X509_TRUSTED_CERTIFICATE_CALLBACK)
    mbedtls_x509_crt_ca_cb_t f_ca_cb;
    void *p_ca_cb;
#endif /* MBEDTLS_X509_TRUSTED_CERTIFICATE_CALLBACK */
#endif /* MBEDTLS_X509_CRT_PARSE_C */

#if defined(MBEDTLS_SSL_ASYNC_PRIVATE)
#if defined(MBEDTLS_X509_CRT_PARSE_C)
    mbedtls_ssl_async_sign_t *f_async_sign_start; /*!< start asynchronous signature operation */
    mbedtls_ssl_async_decrypt_t *f_async_decrypt_start; /*!< start asynchronous decryption operation */
#endif /* MBEDTLS_X509_CRT_PARSE_C */
    mbedtls_ssl_async_resume_t *f_async_resume; /*!< resume asynchronous operation */
    mbedtls_ssl_async_cancel_t *f_async_cancel; /*!< cancel asynchronous operation */
    void *p_async_config_data; /*!< Configuration data set by mbedtls_ssl_conf_async_private_cb(). */
#endif /* MBEDTLS_SSL_ASYNC_PRIVATE */

#if defined(MBEDTLS_KEY_EXCHANGE_WITH_CERT_ENABLED)
    const int *sig_hashes;          /*!< allowed signature hashes           */
#endif

#if defined(MBEDTLS_ECP_C)
    const mbedtls_ecp_group_id *curve_list; /*!< allowed curves             */
#endif

#if defined(MBEDTLS_DHM_C)
    mbedtls_mpi dhm_P;              /*!< prime modulus for DHM              */
    mbedtls_mpi dhm_G;              /*!< generator for DHM                  */
#endif

#if defined(MBEDTLS_KEY_EXCHANGE_SOME_PSK_ENABLED)

#if defined(MBEDTLS_USE_PSA_CRYPTO)
    psa_key_handle_t psk_opaque; /*!< PSA key slot holding opaque PSK.
                                  *   This field should only be set via
                                  *   mbedtls_ssl_conf_psk_opaque().
                                  *   If either no PSK or a raw PSK have
                                  *   been configured, this has value \c 0. */
#endif /* MBEDTLS_USE_PSA_CRYPTO */

    unsigned char *psk;      /*!< The raw pre-shared key. This field should
                              *   only be set via mbedtls_ssl_conf_psk().
                              *   If either no PSK or an opaque PSK
                              *   have been configured, this has value NULL. */
    size_t         psk_len;  /*!< The length of the raw pre-shared key.
                              *   This field should only be set via
                              *   mbedtls_ssl_conf_psk().
                              *   Its value is non-zero if and only if
                              *   \c psk is not \c NULL. */

    unsigned char *psk_identity;    /*!< The PSK identity for PSK negotiation.
                                     *   This field should only be set via
                                     *   mbedtls_ssl_conf_psk().
                                     *   This is set if and only if either
                                     *   \c psk or \c psk_opaque are set. */
    size_t         psk_identity_len;/*!< The length of PSK identity.
                                     *   This field should only be set via
                                     *   mbedtls_ssl_conf_psk().
                                     *   Its value is non-zero if and only if
                                     *   \c psk is not \c NULL or \c psk_opaque
                                     *   is not \c 0. */
#endif /* MBEDTLS_KEY_EXCHANGE_SOME_PSK_ENABLED */

#if defined(MBEDTLS_SSL_ALPN)
    const char **alpn_list;         /*!< ordered list of protocols          */
#endif

    /*
     * Numerical settings (int then char)
     */

    uint32_t read_timeout;          /*!< timeout for mbedtls_ssl_read (ms)  */

#if defined(MBEDTLS_SSL_PROTO_DTLS)
    uint32_t hs_timeout_min;        /*!< initial value of the handshake
                                         retransmission timeout (ms)        */
    uint32_t hs_timeout_max;        /*!< maximum value of the handshake
                                         retransmission timeout (ms)        */
#endif

#if defined(MBEDTLS_SSL_RENEGOTIATION)
    int renego_max_records;         /*!< grace period for renegotiation     */
    unsigned char renego_period[8]; /*!< value of the record counters
                                         that triggers renegotiation        */
#endif

#if defined(MBEDTLS_SSL_DTLS_BADMAC_LIMIT)
    unsigned int badmac_limit;      /*!< limit of records with a bad MAC    */
#endif

#if defined(MBEDTLS_DHM_C) && defined(MBEDTLS_SSL_CLI_C)
    unsigned int dhm_min_bitlen;    /*!< min. bit length of the DHM prime   */
#endif

    unsigned char max_major_ver;    /*!< max. major version used            */
    unsigned char max_minor_ver;    /*!< max. minor version used            */
    unsigned char min_major_ver;    /*!< min. major version used            */
    unsigned char min_minor_ver;    /*!< min. minor version used            */

    /*
     * Flags (bitfields)
     */

    unsigned int endpoint : 1;      /*!< 0: client, 1: server               */
    unsigned int transport : 1;     /*!< stream (TLS) or datagram (DTLS)    */
    unsigned int authmode : 2;      /*!< MBEDTLS_SSL_VERIFY_XXX             */
    /* needed even with renego disabled for LEGACY_BREAK_HANDSHAKE          */
    unsigned int allow_legacy_renegotiation : 2 ; /*!< MBEDTLS_LEGACY_XXX   */
#if defined(MBEDTLS_ARC4_C)
    unsigned int arc4_disabled : 1; /*!< blacklist RC4 ciphersuites?        */
#endif
#if defined(MBEDTLS_SSL_MAX_FRAGMENT_LENGTH)
    unsigned int mfl_code : 3;      /*!< desired fragment length            */
#endif
#if defined(MBEDTLS_SSL_ENCRYPT_THEN_MAC)
    unsigned int encrypt_then_mac : 1 ; /*!< negotiate encrypt-then-mac?    */
#endif
#if defined(MBEDTLS_SSL_EXTENDED_MASTER_SECRET)
    unsigned int extended_ms : 1;   /*!< negotiate extended master secret?  */
#endif
#if defined(MBEDTLS_SSL_DTLS_ANTI_REPLAY)
    unsigned int anti_replay : 1;   /*!< detect and prevent replay?         */
#endif
#if defined(MBEDTLS_SSL_CBC_RECORD_SPLITTING)
    unsigned int cbc_record_splitting : 1;  /*!< do cbc record splitting    */
#endif
#if defined(MBEDTLS_SSL_RENEGOTIATION)
    unsigned int disable_renegotiation : 1; /*!< disable renegotiation?     */
#endif
#if defined(MBEDTLS_SSL_TRUNCATED_HMAC)
    unsigned int trunc_hmac : 1;    /*!< negotiate truncated hmac?          */
#endif
#if defined(MBEDTLS_SSL_SESSION_TICKETS)
    unsigned int session_tickets : 1;   /*!< use session tickets?           */
#endif
#if defined(MBEDTLS_SSL_FALLBACK_SCSV) && defined(MBEDTLS_SSL_CLI_C)
    unsigned int fallback : 1;      /*!< is this a fallback?                */
#endif
#if defined(MBEDTLS_SSL_SRV_C)
    unsigned int cert_req_ca_list : 1;  /*!< enable sending CA list in
                                          Certificate Request messages?     */
#endif
#if defined(MBEDTLS_SSL_DTLS_CONNECTION_ID)
    unsigned int ignore_unexpected_cid : 1; /*!< Determines whether DTLS
                                             *   record with unexpected CID
                                             *   should lead to failure.    */
#endif /* MBEDTLS_SSL_DTLS_CONNECTION_ID */
};


struct mbedtls_ssl_context
{
    const mbedtls_ssl_config *conf; /*!< configuration information          */

    /*
     * Miscellaneous
     */
    int state;                  /*!< SSL handshake: current state     */
#if defined(MBEDTLS_SSL_RENEGOTIATION)
    int renego_status;          /*!< Initial, in progress, pending?   */
    int renego_records_seen;    /*!< Records since renego request, or with DTLS,
                                  number of retransmissions of request if
                                  renego_max_records is < 0           */
#endif /* MBEDTLS_SSL_RENEGOTIATION */

    int major_ver;              /*!< equal to  MBEDTLS_SSL_MAJOR_VERSION_3    */
    int minor_ver;              /*!< either 0 (SSL3) or 1 (TLS1.0)    */

#if defined(MBEDTLS_SSL_DTLS_BADMAC_LIMIT)
    unsigned badmac_seen;       /*!< records with a bad MAC received    */
#endif /* MBEDTLS_SSL_DTLS_BADMAC_LIMIT */

#if defined(MBEDTLS_X509_CRT_PARSE_C)
    /** Callback to customize X.509 certificate chain verification          */
    int (*f_vrfy)(void *, mbedtls_x509_crt *, int, uint32_t *);
    void *p_vrfy;                   /*!< context for X.509 verify callback */
#endif

    mbedtls_ssl_send_t *f_send; /*!< Callback for network send */
    mbedtls_ssl_recv_t *f_recv; /*!< Callback for network receive */
    mbedtls_ssl_recv_timeout_t *f_recv_timeout;
                                /*!< Callback for network receive with timeout */

    void *p_bio;                /*!< context for I/O operations   */

    /*
     * Session layer
     */
    mbedtls_ssl_session *session_in;            /*!<  current session data (in)   */
    mbedtls_ssl_session *session_out;           /*!<  current session data (out)  */
    mbedtls_ssl_session *session;               /*!<  negotiated session data     */
    mbedtls_ssl_session *session_negotiate;     /*!<  session data in negotiation */

    mbedtls_ssl_handshake_params *handshake;    /*!<  params required only during
                                              the handshake process        */

    /*
     * Record layer transformations
     */
    mbedtls_ssl_transform *transform_in;        /*!<  current transform params (in)   */
    mbedtls_ssl_transform *transform_out;       /*!<  current transform params (in)   */
    mbedtls_ssl_transform *transform;           /*!<  negotiated transform params     */
    mbedtls_ssl_transform *transform_negotiate; /*!<  transform params in negotiation */

    /*
     * Timers
     */
    void *p_timer;              /*!< context for the timer callbacks */

    mbedtls_ssl_set_timer_t *f_set_timer;       /*!< set timer callback */
    mbedtls_ssl_get_timer_t *f_get_timer;       /*!< get timer callback */

    /*
     * Record layer (incoming data)
     */
    unsigned char *in_buf;      /*!< input buffer                     */
    unsigned char *in_ctr;      /*!< 64-bit incoming message counter
                                     TLS: maintained by us
                                     DTLS: read from peer             */
    unsigned char *in_hdr;      /*!< start of record header           */
#if defined(MBEDTLS_SSL_DTLS_CONNECTION_ID)
    unsigned char *in_cid;      /*!< The start of the CID;
                                 *   (the end is marked by in_len).   */
#endif /* MBEDTLS_SSL_DTLS_CONNECTION_ID */
    unsigned char *in_len;      /*!< two-bytes message length field   */
    unsigned char *in_iv;       /*!< ivlen-byte IV                    */
    unsigned char *in_msg;      /*!< message contents (in_iv+ivlen)   */
    unsigned char *in_offt;     /*!< read offset in application data  */

    int in_msgtype;             /*!< record header: message type      */
    size_t in_msglen;           /*!< record header: message length    */
    size_t in_left;             /*!< amount of data read so far       */
#if defined(MBEDTLS_SSL_VARIABLE_BUFFER_LENGTH)
    size_t in_buf_len;          /*!< length of input buffer           */
#endif
#if defined(MBEDTLS_SSL_PROTO_DTLS)
    uint16_t in_epoch;          /*!< DTLS epoch for incoming records  */
    size_t next_record_offset;  /*!< offset of the next record in datagram
                                     (equal to in_left if none)       */
#endif /* MBEDTLS_SSL_PROTO_DTLS */
#if defined(MBEDTLS_SSL_DTLS_ANTI_REPLAY)
    uint64_t in_window_top;     /*!< last validated record seq_num    */
    uint64_t in_window;         /*!< bitmask for replay detection     */
#endif /* MBEDTLS_SSL_DTLS_ANTI_REPLAY */

    size_t in_hslen;            /*!< current handshake message length,
                                     including the handshake header   */
    int nb_zero;                /*!< # of 0-length encrypted messages */

    int keep_current_message;   /*!< drop or reuse current message
                                     on next call to record layer? */

#if defined(MBEDTLS_SSL_PROTO_DTLS)
    uint8_t disable_datagram_packing;  /*!< Disable packing multiple records
                                        *   within a single datagram.  */
#endif /* MBEDTLS_SSL_PROTO_DTLS */

    /*
     * Record layer (outgoing data)
     */
    unsigned char *out_buf;     /*!< output buffer                    */
    unsigned char *out_ctr;     /*!< 64-bit outgoing message counter  */
    unsigned char *out_hdr;     /*!< start of record header           */
#if defined(MBEDTLS_SSL_DTLS_CONNECTION_ID)
    unsigned char *out_cid;     /*!< The start of the CID;
                                 *   (the end is marked by in_len).   */
#endif /* MBEDTLS_SSL_DTLS_CONNECTION_ID */
    unsigned char *out_len;     /*!< two-bytes message length field   */
    unsigned char *out_iv;      /*!< ivlen-byte IV                    */
    unsigned char *out_msg;     /*!< message contents (out_iv+ivlen)  */

    int out_msgtype;            /*!< record header: message type      */
    size_t out_msglen;          /*!< record header: message length    */
    size_t out_left;            /*!< amount of data not yet written   */
#if defined(MBEDTLS_SSL_VARIABLE_BUFFER_LENGTH)
    size_t out_buf_len;         /*!< length of output buffer          */
#endif

    unsigned char cur_out_ctr[8]; /*!<  Outgoing record sequence  number. */

#if defined(MBEDTLS_SSL_PROTO_DTLS)
    uint16_t mtu;               /*!< path mtu, used to fragment outgoing messages */
#endif /* MBEDTLS_SSL_PROTO_DTLS */

#if defined(MBEDTLS_ZLIB_SUPPORT)
    unsigned char *compress_buf;        /*!<  zlib data buffer        */
#endif /* MBEDTLS_ZLIB_SUPPORT */
#if defined(MBEDTLS_SSL_CBC_RECORD_SPLITTING)
    signed char split_done;     /*!< current record already splitted? */
#endif /* MBEDTLS_SSL_CBC_RECORD_SPLITTING */

    /*
     * PKI layer
     */
    int client_auth;                    /*!<  flag for client auth.   */

    /*
     * User settings
     */
#if defined(MBEDTLS_X509_CRT_PARSE_C)
    char *hostname;             /*!< expected peer CN for verification
                                     (and SNI if available)                 */
#endif /* MBEDTLS_X509_CRT_PARSE_C */

#if defined(MBEDTLS_SSL_ALPN)
    const char *alpn_chosen;    /*!<  negotiated protocol                   */
#endif /* MBEDTLS_SSL_ALPN */

    /*
     * Information for DTLS hello verify
     */
#if defined(MBEDTLS_SSL_DTLS_HELLO_VERIFY) && defined(MBEDTLS_SSL_SRV_C)
    unsigned char  *cli_id;         /*!<  transport-level ID of the client  */
    size_t          cli_id_len;     /*!<  length of cli_id                  */
#endif /* MBEDTLS_SSL_DTLS_HELLO_VERIFY && MBEDTLS_SSL_SRV_C */

    /*
     * Secure renegotiation
     */
    /* needed to know when to send extension on server */
    int secure_renegotiation;           /*!<  does peer support legacy or
                                              secure renegotiation           */
#if defined(MBEDTLS_SSL_RENEGOTIATION)
    size_t verify_data_len;             /*!<  length of verify data stored   */
    char own_verify_data[MBEDTLS_SSL_VERIFY_DATA_MAX_LEN]; /*!<  previous handshake verify data */
    char peer_verify_data[MBEDTLS_SSL_VERIFY_DATA_MAX_LEN]; /*!<  previous handshake verify data */
#endif /* MBEDTLS_SSL_RENEGOTIATION */

#if defined(MBEDTLS_SSL_DTLS_CONNECTION_ID)
    /* CID configuration to use in subsequent handshakes. */

    /*! The next incoming CID, chosen by the user and applying to
     *  all subsequent handshakes. This may be different from the
     *  CID currently used in case the user has re-configured the CID
     *  after an initial handshake. */
    unsigned char own_cid[ MBEDTLS_SSL_CID_IN_LEN_MAX ];
    uint8_t own_cid_len;   /*!< The length of \c own_cid. */
    uint8_t negotiate_cid; /*!< This indicates whether the CID extension should
                            *   be negotiated in the next handshake or not.
                            *   Possible values are #MBEDTLS_SSL_CID_ENABLED
                            *   and #MBEDTLS_SSL_CID_DISABLED. */
#endif /* MBEDTLS_SSL_DTLS_CONNECTION_ID */
};

#if defined(MBEDTLS_SSL_HW_RECORD_ACCEL)

#if !defined(MBEDTLS_DEPRECATED_REMOVED)

#define MBEDTLS_SSL_CHANNEL_OUTBOUND   MBEDTLS_DEPRECATED_NUMERIC_CONSTANT( 0 )
#define MBEDTLS_SSL_CHANNEL_INBOUND    MBEDTLS_DEPRECATED_NUMERIC_CONSTANT( 1 )

#if defined(MBEDTLS_DEPRECATED_WARNING)
#define MBEDTLS_DEPRECATED      __attribute__((deprecated))
#else
#define MBEDTLS_DEPRECATED
#endif /* MBEDTLS_DEPRECATED_WARNING */

MBEDTLS_DEPRECATED extern int (*mbedtls_ssl_hw_record_init)(
                    mbedtls_ssl_context *ssl,
                    const unsigned char *key_enc, const unsigned char *key_dec,
                    size_t keylen,
                    const unsigned char *iv_enc,  const unsigned char *iv_dec,
                    size_t ivlen,
                    const unsigned char *mac_enc, const unsigned char *mac_dec,
                    size_t maclen);
MBEDTLS_DEPRECATED extern int (*mbedtls_ssl_hw_record_activate)(
                                                    mbedtls_ssl_context *ssl,
                                                    int direction );
MBEDTLS_DEPRECATED extern int (*mbedtls_ssl_hw_record_reset)(
                                                    mbedtls_ssl_context *ssl );
MBEDTLS_DEPRECATED extern int (*mbedtls_ssl_hw_record_write)(
                                                    mbedtls_ssl_context *ssl );
MBEDTLS_DEPRECATED extern int (*mbedtls_ssl_hw_record_read)(
                                                    mbedtls_ssl_context *ssl );
MBEDTLS_DEPRECATED extern int (*mbedtls_ssl_hw_record_finish)(
                                                    mbedtls_ssl_context *ssl );

#undef MBEDTLS_DEPRECATED
#endif /* !MBEDTLS_DEPRECATED_REMOVED */

#endif /* MBEDTLS_SSL_HW_RECORD_ACCEL */

/**
 * \brief               Return the name of the ciphersuite associated with the
 *                      given ID
 *
 * \param ciphersuite_id SSL ciphersuite ID
 *
 * \return              a string containing the ciphersuite name
 */
const char *mbedtls_ssl_get_ciphersuite_name( const int ciphersuite_id );

/**
 * \brief               Return the ID of the ciphersuite associated with the
 *                      given name
 *
 * \param ciphersuite_name SSL ciphersuite name
 *
 * \return              the ID with the ciphersuite or 0 if not found
 */
int mbedtls_ssl_get_ciphersuite_id( const char *ciphersuite_name );

/**
 * \brief          Initialize an SSL context
 *                 Just makes the context ready for mbedtls_ssl_setup() or
 *                 mbedtls_ssl_free()
 *
 * \param ssl      SSL context
 */
void mbedtls_ssl_init( mbedtls_ssl_context *ssl );

/**
 * \brief          Set up an SSL context for use
 *
 * \note           No copy of the configuration context is made, it can be
 *                 shared by many mbedtls_ssl_context structures.
 *
 * \warning        The conf structure will be accessed during the session.
 *                 It must not be modified or freed as long as the session
 *                 is active.
 *
 * \warning        This function must be called exactly once per context.
 *                 Calling mbedtls_ssl_setup again is not supported, even
 *                 if no session is active.
 *
 * \param ssl      SSL context
 * \param conf     SSL configuration to use
 *
 * \return         0 if successful, or MBEDTLS_ERR_SSL_ALLOC_FAILED if
 *                 memory allocation failed
 */
int mbedtls_ssl_setup( mbedtls_ssl_context *ssl,
                       const mbedtls_ssl_config *conf );

/**
 * \brief          Reset an already initialized SSL context for re-use
 *                 while retaining application-set variables, function
 *                 pointers and data.
 *
 * \param ssl      SSL context
 * \return         0 if successful, or MBEDTLS_ERR_SSL_ALLOC_FAILED,
                   MBEDTLS_ERR_SSL_HW_ACCEL_FAILED or
 *                 MBEDTLS_ERR_SSL_COMPRESSION_FAILED
 */
int mbedtls_ssl_session_reset( mbedtls_ssl_context *ssl );

/**
 * \brief          Set the current endpoint type
 *
 * \param conf     SSL configuration
 * \param endpoint must be MBEDTLS_SSL_IS_CLIENT or MBEDTLS_SSL_IS_SERVER
 */
void mbedtls_ssl_conf_endpoint( mbedtls_ssl_config *conf, int endpoint );

/**
 * \brief           Set the transport type (TLS or DTLS).
 *                  Default: TLS
 *
 * \note            For DTLS, you must either provide a recv callback that
 *                  doesn't block, or one that handles timeouts, see
 *                  \c mbedtls_ssl_set_bio(). You also need to provide timer
 *                  callbacks with \c mbedtls_ssl_set_timer_cb().
 *
 * \param conf      SSL configuration
 * \param transport transport type:
 *                  MBEDTLS_SSL_TRANSPORT_STREAM for TLS,
 *                  MBEDTLS_SSL_TRANSPORT_DATAGRAM for DTLS.
 */
void mbedtls_ssl_conf_transport( mbedtls_ssl_config *conf, int transport );

/**
 * \brief          Set the certificate verification mode
 *                 Default: NONE on server, REQUIRED on client
 *
 * \param conf     SSL configuration
 * \param authmode can be:
 *
 *  MBEDTLS_SSL_VERIFY_NONE:      peer certificate is not checked
 *                        (default on server)
 *                        (insecure on client)
 *
 *  MBEDTLS_SSL_VERIFY_OPTIONAL:  peer certificate is checked, however the
 *                        handshake continues even if verification failed;
 *                        mbedtls_ssl_get_verify_result() can be called after the
 *                        handshake is complete.
 *
 *  MBEDTLS_SSL_VERIFY_REQUIRED:  peer *must* present a valid certificate,
 *                        handshake is aborted if verification failed.
 *                        (default on client)
 *
 * \note On client, MBEDTLS_SSL_VERIFY_REQUIRED is the recommended mode.
 * With MBEDTLS_SSL_VERIFY_OPTIONAL, the user needs to call mbedtls_ssl_get_verify_result() at
 * the right time(s), which may not be obvious, while REQUIRED always perform
 * the verification as soon as possible. For example, REQUIRED was protecting
 * against the "triple handshake" attack even before it was found.
 */
void mbedtls_ssl_conf_authmode( mbedtls_ssl_config *conf, int authmode );

#if defined(MBEDTLS_X509_CRT_PARSE_C)
/**
 * \brief          Set the verification callback (Optional).
 *
 *                 If set, the provided verify callback is called for each
 *                 certificate in the peer's CRT chain, including the trusted
 *                 root. For more information, please see the documentation of
 *                 \c mbedtls_x509_crt_verify().
 *
 * \note           For per context callbacks and contexts, please use
 *                 mbedtls_ssl_set_verify() instead.
 *
 * \param conf     The SSL configuration to use.
 * \param f_vrfy   The verification callback to use during CRT verification.
 * \param p_vrfy   The opaque context to be passed to the callback.
 */
void mbedtls_ssl_conf_verify( mbedtls_ssl_config *conf,
                     int (*f_vrfy)(void *, mbedtls_x509_crt *, int, uint32_t *),
                     void *p_vrfy );
#endif /* MBEDTLS_X509_CRT_PARSE_C */

/**
 * \brief          Set the random number generator callback
 *
 * \param conf     SSL configuration
 * \param f_rng    RNG function
 * \param p_rng    RNG parameter
 */
void mbedtls_ssl_conf_rng( mbedtls_ssl_config *conf,
                  int (*f_rng)(void *, unsigned char *, size_t),
                  void *p_rng );

/**
 * \brief          Set the debug callback
 *
 *                 The callback has the following argument:
 *                 void *           opaque context for the callback
 *                 int              debug level
 *                 const char *     file name
 *                 int              line number
 *                 const char *     message
 *
 * \param conf     SSL configuration
 * \param f_dbg    debug function
 * \param p_dbg    debug parameter
 */
void mbedtls_ssl_conf_dbg( mbedtls_ssl_config *conf,
                  void (*f_dbg)(void *, int, const char *, int, const char *),
                  void  *p_dbg );

/**
 * \brief          Set the underlying BIO callbacks for write, read and
 *                 read-with-timeout.
 *
 * \param ssl      SSL context
 * \param p_bio    parameter (context) shared by BIO callbacks
 * \param f_send   write callback
 * \param f_recv   read callback
 * \param f_recv_timeout blocking read callback with timeout.
 *
 * \note           One of f_recv or f_recv_timeout can be NULL, in which case
 *                 the other is used. If both are non-NULL, f_recv_timeout is
 *                 used and f_recv is ignored (as if it were NULL).
 *
 * \note           The two most common use cases are:
 *                 - non-blocking I/O, f_recv != NULL, f_recv_timeout == NULL
 *                 - blocking I/O, f_recv == NULL, f_recv_timout != NULL
 *
 * \note           For DTLS, you need to provide either a non-NULL
 *                 f_recv_timeout callback, or a f_recv that doesn't block.
 *
 * \note           See the documentations of \c mbedtls_ssl_sent_t,
 *                 \c mbedtls_ssl_recv_t and \c mbedtls_ssl_recv_timeout_t for
 *                 the conventions those callbacks must follow.
 *
 * \note           On some platforms, net_sockets.c provides
 *                 \c mbedtls_net_send(), \c mbedtls_net_recv() and
 *                 \c mbedtls_net_recv_timeout() that are suitable to be used
 *                 here.
 */
void mbedtls_ssl_set_bio( mbedtls_ssl_context *ssl,
                          void *p_bio,
                          mbedtls_ssl_send_t *f_send,
                          mbedtls_ssl_recv_t *f_recv,
                          mbedtls_ssl_recv_timeout_t *f_recv_timeout );

#if defined(MBEDTLS_SSL_PROTO_DTLS)

#if defined(MBEDTLS_SSL_DTLS_CONNECTION_ID)


/**
 * \brief             Configure the use of the Connection ID (CID)
 *                    extension in the next handshake.
 *
 *                    Reference: draft-ietf-tls-dtls-connection-id-05
 *                    https://tools.ietf.org/html/draft-ietf-tls-dtls-connection-id-05
 *
 *                    The DTLS CID extension allows the reliable association of
 *                    DTLS records to DTLS connections across changes in the
 *                    underlying transport (changed IP and Port metadata) by
 *                    adding explicit connection identifiers (CIDs) to the
 *                    headers of encrypted DTLS records. The desired CIDs are
 *                    configured by the application layer and are exchanged in
 *                    new `ClientHello` / `ServerHello` extensions during the
 *                    handshake, where each side indicates the CID it wants the
 *                    peer to use when writing encrypted messages. The CIDs are
 *                    put to use once records get encrypted: the stack discards
 *                    any incoming records that don't include the configured CID
 *                    in their header, and adds the peer's requested CID to the
 *                    headers of outgoing messages.
 *
 *                    This API enables or disables the use of the CID extension
 *                    in the next handshake and sets the value of the CID to
 *                    be used for incoming messages.
 *
 * \param ssl         The SSL context to configure. This must be initialized.
 * \param enable      This value determines whether the CID extension should
 *                    be used or not. Possible values are:
 *                    - MBEDTLS_SSL_CID_ENABLED to enable the use of the CID.
 *                    - MBEDTLS_SSL_CID_DISABLED (default) to disable the use
 *                      of the CID.
 * \param own_cid     The address of the readable buffer holding the CID we want
 *                    the peer to use when sending encrypted messages to us.
 *                    This may be \c NULL if \p own_cid_len is \c 0.
 *                    This parameter is unused if \p enabled is set to
 *                    MBEDTLS_SSL_CID_DISABLED.
 * \param own_cid_len The length of \p own_cid.
 *                    This parameter is unused if \p enabled is set to
 *                    MBEDTLS_SSL_CID_DISABLED.
 *
 * \note              The value of \p own_cid_len must match the value of the
 *                    \c len parameter passed to mbedtls_ssl_conf_cid()
 *                    when configuring the ::mbedtls_ssl_config that \p ssl
 *                    is bound to.
 *
 * \note              This CID configuration applies to subsequent handshakes
 *                    performed on the SSL context \p ssl, but does not trigger
 *                    one. You still have to call `mbedtls_ssl_handshake()`
 *                    (for the initial handshake) or `mbedtls_ssl_renegotiate()`
 *                    (for a renegotiation handshake) explicitly after a
 *                    successful call to this function to run the handshake.
 *
 * \note              This call cannot guarantee that the use of the CID
 *                    will be successfully negotiated in the next handshake,
 *                    because the peer might not support it. Specifically:
 *                    - On the Client, enabling the use of the CID through
 *                      this call implies that the `ClientHello` in the next
 *                      handshake will include the CID extension, thereby
 *                      offering the use of the CID to the server. Only if
 *                      the `ServerHello` contains the CID extension, too,
 *                      the CID extension will actually be put to use.
 *                    - On the Server, enabling the use of the CID through
 *                      this call implies that that the server will look for
 *                      the CID extension in a `ClientHello` from the client,
 *                      and, if present, reply with a CID extension in its
 *                      `ServerHello`.
 *
 * \note              To check whether the use of the CID was negotiated
 *                    after the subsequent handshake has completed, please
 *                    use the API mbedtls_ssl_get_peer_cid().
 *
 * \warning           If the use of the CID extension is enabled in this call
 *                    and the subsequent handshake negotiates its use, Mbed TLS
 *                    will silently drop every packet whose CID does not match
 *                    the CID configured in \p own_cid. It is the responsibility
 *                    of the user to adapt the underlying transport to take care
 *                    of CID-based demultiplexing before handing datagrams to
 *                    Mbed TLS.
 *
 * \return            \c 0 on success. In this case, the CID configuration
 *                    applies to the next handshake.
 * \return            A negative error code on failure.
 */
int mbedtls_ssl_set_cid( mbedtls_ssl_context *ssl,
                         int enable,
                         unsigned char const *own_cid,
                         size_t own_cid_len );

/**
 * \brief              Get information about the use of the CID extension
 *                     in the current connection.
 *
 * \param ssl          The SSL context to query.
 * \param enabled      The address at which to store whether the CID extension
 *                     is currently in use or not. If the CID is in use,
 *                     `*enabled` is set to MBEDTLS_SSL_CID_ENABLED;
 *                     otherwise, it is set to MBEDTLS_SSL_CID_DISABLED.
 * \param peer_cid     The address of the buffer in which to store the CID
 *                     chosen by the peer (if the CID extension is used).
 *                     This may be \c NULL in case the value of peer CID
 *                     isn't needed. If it is not \c NULL, \p peer_cid_len
 *                     must not be \c NULL.
 * \param peer_cid_len The address at which to store the size of the CID
 *                     chosen by the peer (if the CID extension is used).
 *                     This is also the number of Bytes in \p peer_cid that
 *                     have been written.
 *                     This may be \c NULL in case the length of the peer CID
 *                     isn't needed. If it is \c NULL, \p peer_cid must be
 *                     \c NULL, too.
 *
 * \note               This applies to the state of the CID negotiated in
 *                     the last complete handshake. If a handshake is in
 *                     progress, this function will attempt to complete
 *                     the handshake first.
 *
 * \note               If CID extensions have been exchanged but both client
 *                     and server chose to use an empty CID, this function
 *                     sets `*enabled` to #MBEDTLS_SSL_CID_DISABLED
 *                     (the rationale for this is that the resulting
 *                     communication is the same as if the CID extensions
 *                     hadn't been used).
 *
 * \return            \c 0 on success.
 * \return            A negative error code on failure.
 */
int mbedtls_ssl_get_peer_cid( mbedtls_ssl_context *ssl,
                     int *enabled,
                     unsigned char peer_cid[ MBEDTLS_SSL_CID_OUT_LEN_MAX ],
                     size_t *peer_cid_len );

#endif /* MBEDTLS_SSL_DTLS_CONNECTION_ID */

/**
 * \brief          Set the Maximum Tranport Unit (MTU).
 *                 Special value: 0 means unset (no limit).
 *                 This represents the maximum size of a datagram payload
 *                 handled by the transport layer (usually UDP) as determined
 *                 by the network link and stack. In practice, this controls
 *                 the maximum size datagram the DTLS layer will pass to the
 *                 \c f_send() callback set using \c mbedtls_ssl_set_bio().
 *
 * \note           The limit on datagram size is converted to a limit on
 *                 record payload by subtracting the current overhead of
 *                 encapsulation and encryption/authentication if any.
 *
 * \note           This can be called at any point during the connection, for
 *                 example when a Path Maximum Transfer Unit (PMTU)
 *                 estimate becomes available from other sources,
 *                 such as lower (or higher) protocol layers.
 *
 * \note           This setting only controls the size of the packets we send,
 *                 and does not restrict the size of the datagrams we're
 *                 willing to receive. Client-side, you can request the
 *                 server to use smaller records with \c
 *                 mbedtls_ssl_conf_max_frag_len().
 *
 * \note           If both a MTU and a maximum fragment length have been
 *                 configured (or negotiated with the peer), the resulting
 *                 lower limit on record payload (see first note) is used.
 *
 * \note           This can only be used to decrease the maximum size
 *                 of datagrams (hence records, see first note) sent. It
 *                 cannot be used to increase the maximum size of records over
 *                 the limit set by #MBEDTLS_SSL_OUT_CONTENT_LEN.
 *
 * \note           Values lower than the current record layer expansion will
 *                 result in an error when trying to send data.
 *
 * \note           Using record compression together with a non-zero MTU value
 *                 will result in an error when trying to send data.
 *
 * \param ssl      SSL context
 * \param mtu      Value of the path MTU in bytes
 */
void mbedtls_ssl_set_mtu( mbedtls_ssl_context *ssl, uint16_t mtu );
#endif /* MBEDTLS_SSL_PROTO_DTLS */

#if defined(MBEDTLS_X509_CRT_PARSE_C)
/**
 * \brief          Set a connection-specific verification callback (optional).
 *
 *                 If set, the provided verify callback is called for each
 *                 certificate in the peer's CRT chain, including the trusted
 *                 root. For more information, please see the documentation of
 *                 \c mbedtls_x509_crt_verify().
 *
 * \note           This call is analogous to mbedtls_ssl_conf_verify() but
 *                 binds the verification callback and context to an SSL context
 *                 as opposed to an SSL configuration.
 *                 If mbedtls_ssl_conf_verify() and mbedtls_ssl_set_verify()
 *                 are both used, mbedtls_ssl_set_verify() takes precedence.
 *
 * \param ssl      The SSL context to use.
 * \param f_vrfy   The verification callback to use during CRT verification.
 * \param p_vrfy   The opaque context to be passed to the callback.
 */
void mbedtls_ssl_set_verify( mbedtls_ssl_context *ssl,
                     int (*f_vrfy)(void *, mbedtls_x509_crt *, int, uint32_t *),
                     void *p_vrfy );
#endif /* MBEDTLS_X509_CRT_PARSE_C */

/**
 * \brief          Set the timeout period for mbedtls_ssl_read()
 *                 (Default: no timeout.)
 *
 * \param conf     SSL configuration context
 * \param timeout  Timeout value in milliseconds.
 *                 Use 0 for no timeout (default).
 *
 * \note           With blocking I/O, this will only work if a non-NULL
 *                 \c f_recv_timeout was set with \c mbedtls_ssl_set_bio().
 *                 With non-blocking I/O, this will only work if timer
 *                 callbacks were set with \c mbedtls_ssl_set_timer_cb().
 *
 * \note           With non-blocking I/O, you may also skip this function
 *                 altogether and handle timeouts at the application layer.
 */
void mbedtls_ssl_conf_read_timeout( mbedtls_ssl_config *conf, uint32_t timeout );

#if defined(MBEDTLS_SSL_RECORD_CHECKING)
/**
 * \brief          Check whether a buffer contains a valid and authentic record
 *                 that has not been seen before. (DTLS only).
 *
 *                 This function does not change the user-visible state
 *                 of the SSL context. Its sole purpose is to provide
 *                 an indication of the legitimacy of an incoming record.
 *
 *                 This can be useful e.g. in distributed server environments
 *                 using the DTLS Connection ID feature, in which connections
 *                 might need to be passed between service instances on a change
 *                 of peer address, but where such disruptive operations should
 *                 only happen after the validity of incoming records has been
 *                 confirmed.
 *
 * \param ssl      The SSL context to use.
 * \param buf      The address of the buffer holding the record to be checked.
 *                 This must be a read/write buffer of length \p buflen Bytes.
 * \param buflen   The length of \p buf in Bytes.
 *
 * \note           This routine only checks whether the provided buffer begins
 *                 with a valid and authentic record that has not been seen
 *                 before, but does not check potential data following the
 *                 initial record. In particular, it is possible to pass DTLS
 *                 datagrams containing multiple records, in which case only
 *                 the first record is checked.
 *
 * \note           This function modifies the input buffer \p buf. If you need
 *                 to preserve the original record, you have to maintain a copy.
 *
 * \return         \c 0 if the record is valid and authentic and has not been
 *                 seen before.
 * \return         MBEDTLS_ERR_SSL_INVALID_MAC if the check completed
 *                 successfully but the record was found to be not authentic.
 * \return         MBEDTLS_ERR_SSL_INVALID_RECORD if the check completed
 *                 successfully but the record was found to be invalid for
 *                 a reason different from authenticity checking.
 * \return         MBEDTLS_ERR_SSL_UNEXPECTED_RECORD if the check completed
 *                 successfully but the record was found to be unexpected
 *                 in the state of the SSL context, including replayed records.
 * \return         Another negative error code on different kinds of failure.
 *                 In this case, the SSL context becomes unusable and needs
 *                 to be freed or reset before reuse.
 */
int mbedtls_ssl_check_record( mbedtls_ssl_context const *ssl,
                              unsigned char *buf,
                              size_t buflen );
#endif /* MBEDTLS_SSL_RECORD_CHECKING */

/**
 * \brief          Set the timer callbacks (Mandatory for DTLS.)
 *
 * \param ssl      SSL context
 * \param p_timer  parameter (context) shared by timer callbacks
 * \param f_set_timer   set timer callback
 * \param f_get_timer   get timer callback. Must return:
 *
 * \note           See the documentation of \c mbedtls_ssl_set_timer_t and
 *                 \c mbedtls_ssl_get_timer_t for the conventions this pair of
 *                 callbacks must follow.
 *
 * \note           On some platforms, timing.c provides
 *                 \c mbedtls_timing_set_delay() and
 *                 \c mbedtls_timing_get_delay() that are suitable for using
 *                 here, except if using an event-driven style.
 *
 * \note           See also the "DTLS tutorial" article in our knowledge base.
 *                 https://tls.mbed.org/kb/how-to/dtls-tutorial
 */
void mbedtls_ssl_set_timer_cb( mbedtls_ssl_context *ssl,
                               void *p_timer,
                               mbedtls_ssl_set_timer_t *f_set_timer,
                               mbedtls_ssl_get_timer_t *f_get_timer );

/**
 * \brief           Callback type: generate and write session ticket
 *
 * \note            This describes what a callback implementation should do.
 *                  This callback should generate an encrypted and
 *                  authenticated ticket for the session and write it to the
 *                  output buffer. Here, ticket means the opaque ticket part
 *                  of the NewSessionTicket structure of RFC 5077.
 *
 * \param p_ticket  Context for the callback
 * \param session   SSL session to be written in the ticket
 * \param start     Start of the output buffer
 * \param end       End of the output buffer
 * \param tlen      On exit, holds the length written
 * \param lifetime  On exit, holds the lifetime of the ticket in seconds
 *
 * \return          0 if successful, or
 *                  a specific MBEDTLS_ERR_XXX code.
 */
typedef int mbedtls_ssl_ticket_write_t( void *p_ticket,
                                        const mbedtls_ssl_session *session,
                                        unsigned char *start,
                                        const unsigned char *end,
                                        size_t *tlen,
                                        uint32_t *lifetime );

#if defined(MBEDTLS_SSL_EXPORT_KEYS)
/**
 * \brief           Callback type: Export key block and master secret
 *
 * \note            This is required for certain uses of TLS, e.g. EAP-TLS
 *                  (RFC 5216) and Thread. The key pointers are ephemeral and
 *                  therefore must not be stored. The master secret and keys
 *                  should not be used directly except as an input to a key
 *                  derivation function.
 *
 * \param p_expkey  Context for the callback
 * \param ms        Pointer to master secret (fixed length: 48 bytes)
 * \param kb        Pointer to key block, see RFC 5246 section 6.3
 *                  (variable length: 2 * maclen + 2 * keylen + 2 * ivlen).
 * \param maclen    MAC length
 * \param keylen    Key length
 * \param ivlen     IV length
 *
 * \return          0 if successful, or
 *                  a specific MBEDTLS_ERR_XXX code.
 */
typedef int mbedtls_ssl_export_keys_t( void *p_expkey,
                                const unsigned char *ms,
                                const unsigned char *kb,
                                size_t maclen,
                                size_t keylen,
                                size_t ivlen );

/**
 * \brief           Callback type: Export key block, master secret,
 *                                 handshake randbytes and the tls_prf function
 *                                 used to derive keys.
 *
 * \note            This is required for certain uses of TLS, e.g. EAP-TLS
 *                  (RFC 5216) and Thread. The key pointers are ephemeral and
 *                  therefore must not be stored. The master secret and keys
 *                  should not be used directly except as an input to a key
 *                  derivation function.
 *
 * \param p_expkey  Context for the callback.
 * \param ms        Pointer to master secret (fixed length: 48 bytes).
 * \param kb            Pointer to key block, see RFC 5246 section 6.3.
 *                      (variable length: 2 * maclen + 2 * keylen + 2 * ivlen).
 * \param maclen        MAC length.
 * \param keylen        Key length.
 * \param ivlen         IV length.
 * \param client_random The client random bytes.
 * \param server_random The server random bytes.
 * \param tls_prf_type The tls_prf enum type.
 *
 * \return          0 if successful, or
 *                  a specific MBEDTLS_ERR_XXX code.
 */
typedef int mbedtls_ssl_export_keys_ext_t( void *p_expkey,
                                           const unsigned char *ms,
                                           const unsigned char *kb,
                                           size_t maclen,
                                           size_t keylen,
                                           size_t ivlen,
                                           const unsigned char client_random[32],
                                           const unsigned char server_random[32],
                                           mbedtls_tls_prf_types tls_prf_type );
#endif /* MBEDTLS_SSL_EXPORT_KEYS */

/**
 * \brief           Callback type: parse and load session ticket
 *
 * \note            This describes what a callback implementation should do.
 *                  This callback should parse a session ticket as generated
 *                  by the corresponding mbedtls_ssl_ticket_write_t function,
 *                  and, if the ticket is authentic and valid, load the
 *                  session.
 *
 * \note            The implementation is allowed to modify the first len
 *                  bytes of the input buffer, eg to use it as a temporary
 *                  area for the decrypted ticket contents.
 *
 * \param p_ticket  Context for the callback
 * \param session   SSL session to be loaded
 * \param buf       Start of the buffer containing the ticket
 * \param len       Length of the ticket.
 *
 * \return          0 if successful, or
 *                  MBEDTLS_ERR_SSL_INVALID_MAC if not authentic, or
 *                  MBEDTLS_ERR_SSL_SESSION_TICKET_EXPIRED if expired, or
 *                  any other non-zero code for other failures.
 */
typedef int mbedtls_ssl_ticket_parse_t( void *p_ticket,
                                        mbedtls_ssl_session *session,
                                        unsigned char *buf,
                                        size_t len );

#if defined(MBEDTLS_SSL_SESSION_TICKETS) && defined(MBEDTLS_SSL_SRV_C)
/**
 * \brief           Configure SSL session ticket callbacks (server only).
 *                  (Default: none.)
 *
 * \note            On server, session tickets are enabled by providing
 *                  non-NULL callbacks.
 *
 * \note            On client, use \c mbedtls_ssl_conf_session_tickets().
 *
 * \param conf      SSL configuration context
 * \param f_ticket_write    Callback for writing a ticket
 * \param f_ticket_parse    Callback for parsing a ticket
 * \param p_ticket          Context shared by the two callbacks
 */
void mbedtls_ssl_conf_session_tickets_cb( mbedtls_ssl_config *conf,
        mbedtls_ssl_ticket_write_t *f_ticket_write,
        mbedtls_ssl_ticket_parse_t *f_ticket_parse,
        void *p_ticket );
#endif /* MBEDTLS_SSL_SESSION_TICKETS && MBEDTLS_SSL_SRV_C */

#if defined(MBEDTLS_SSL_EXPORT_KEYS)
/**
 * \brief           Configure key export callback.
 *                  (Default: none.)
 *
 * \note            See \c mbedtls_ssl_export_keys_t.
 *
 * \param conf      SSL configuration context
 * \param f_export_keys     Callback for exporting keys
 * \param p_export_keys     Context for the callback
 */
void mbedtls_ssl_conf_export_keys_cb( mbedtls_ssl_config *conf,
        mbedtls_ssl_export_keys_t *f_export_keys,
        void *p_export_keys );

/**
 * \brief           Configure extended key export callback.
 *                  (Default: none.)
 *
 * \note            See \c mbedtls_ssl_export_keys_ext_t.
 *
 * \param conf      SSL configuration context
 * \param f_export_keys_ext Callback for exporting keys
 * \param p_export_keys     Context for the callback
 */
void mbedtls_ssl_conf_export_keys_ext_cb( mbedtls_ssl_config *conf,
        mbedtls_ssl_export_keys_ext_t *f_export_keys_ext,
        void *p_export_keys );
#endif /* MBEDTLS_SSL_EXPORT_KEYS */

#if defined(MBEDTLS_SSL_ASYNC_PRIVATE)
/**
 * \brief           Configure asynchronous private key operation callbacks.
 *
 * \param conf              SSL configuration context
 * \param f_async_sign      Callback to start a signature operation. See
 *                          the description of ::mbedtls_ssl_async_sign_t
 *                          for more information. This may be \c NULL if the
 *                          external processor does not support any signature
 *                          operation; in this case the private key object
 *                          associated with the certificate will be used.
 * \param f_async_decrypt   Callback to start a decryption operation. See
 *                          the description of ::mbedtls_ssl_async_decrypt_t
 *                          for more information. This may be \c NULL if the
 *                          external processor does not support any decryption
 *                          operation; in this case the private key object
 *                          associated with the certificate will be used.
 * \param f_async_resume    Callback to resume an asynchronous operation. See
 *                          the description of ::mbedtls_ssl_async_resume_t
 *                          for more information. This may not be \c NULL unless
 *                          \p f_async_sign and \p f_async_decrypt are both
 *                          \c NULL.
 * \param f_async_cancel    Callback to cancel an asynchronous operation. See
 *                          the description of ::mbedtls_ssl_async_cancel_t
 *                          for more information. This may be \c NULL if
 *                          no cleanup is needed.
 * \param config_data       A pointer to configuration data which can be
 *                          retrieved with
 *                          mbedtls_ssl_conf_get_async_config_data(). The
 *                          library stores this value without dereferencing it.
 */
void mbedtls_ssl_conf_async_private_cb( mbedtls_ssl_config *conf,
                                        mbedtls_ssl_async_sign_t *f_async_sign,
                                        mbedtls_ssl_async_decrypt_t *f_async_decrypt,
                                        mbedtls_ssl_async_resume_t *f_async_resume,
                                        mbedtls_ssl_async_cancel_t *f_async_cancel,
                                        void *config_data );

/**
 * \brief           Retrieve the configuration data set by
 *                  mbedtls_ssl_conf_async_private_cb().
 *
 * \param conf      SSL configuration context
 * \return          The configuration data set by
 *                  mbedtls_ssl_conf_async_private_cb().
 */
void *mbedtls_ssl_conf_get_async_config_data( const mbedtls_ssl_config *conf );

/**
 * \brief           Retrieve the asynchronous operation user context.
 *
 * \note            This function may only be called while a handshake
 *                  is in progress.
 *
 * \param ssl       The SSL context to access.
 *
 * \return          The asynchronous operation user context that was last
 *                  set during the current handshake. If
 *                  mbedtls_ssl_set_async_operation_data() has not yet been
 *                  called during the current handshake, this function returns
 *                  \c NULL.
 */
void *mbedtls_ssl_get_async_operation_data( const mbedtls_ssl_context *ssl );

/**
 * \brief           Retrieve the asynchronous operation user context.
 *
 * \note            This function may only be called while a handshake
 *                  is in progress.
 *
 * \param ssl       The SSL context to access.
 * \param ctx       The new value of the asynchronous operation user context.
 *                  Call mbedtls_ssl_get_async_operation_data() later during the
 *                  same handshake to retrieve this value.
 */
void mbedtls_ssl_set_async_operation_data( mbedtls_ssl_context *ssl,
                                 void *ctx );
#endif /* MBEDTLS_SSL_ASYNC_PRIVATE */

/**
 * \brief          Callback type: generate a cookie
 *
 * \param ctx      Context for the callback
 * \param p        Buffer to write to,
 *                 must be updated to point right after the cookie
 * \param end      Pointer to one past the end of the output buffer
 * \param info     Client ID info that was passed to
 *                 \c mbedtls_ssl_set_client_transport_id()
 * \param ilen     Length of info in bytes
 *
 * \return         The callback must return 0 on success,
 *                 or a negative error code.
 */
typedef int mbedtls_ssl_cookie_write_t( void *ctx,
                                unsigned char **p, unsigned char *end,
                                const unsigned char *info, size_t ilen );

/**
 * \brief          Callback type: verify a cookie
 *
 * \param ctx      Context for the callback
 * \param cookie   Cookie to verify
 * \param clen     Length of cookie
 * \param info     Client ID info that was passed to
 *                 \c mbedtls_ssl_set_client_transport_id()
 * \param ilen     Length of info in bytes
 *
 * \return         The callback must return 0 if cookie is valid,
 *                 or a negative error code.
 */
typedef int mbedtls_ssl_cookie_check_t( void *ctx,
                                const unsigned char *cookie, size_t clen,
                                const unsigned char *info, size_t ilen );

#if defined(MBEDTLS_SSL_DTLS_HELLO_VERIFY) && defined(MBEDTLS_SSL_SRV_C)
/**
 * \brief           Register callbacks for DTLS cookies
 *                  (Server only. DTLS only.)
 *
 *                  Default: dummy callbacks that fail, in order to force you to
 *                  register working callbacks (and initialize their context).
 *
 *                  To disable HelloVerifyRequest, register NULL callbacks.
 *
 * \warning         Disabling hello verification allows your server to be used
 *                  for amplification in DoS attacks against other hosts.
 *                  Only disable if you known this can't happen in your
 *                  particular environment.
 *
 * \note            See comments on \c mbedtls_ssl_handshake() about handling
 *                  the MBEDTLS_ERR_SSL_HELLO_VERIFY_REQUIRED that is expected
 *                  on the first handshake attempt when this is enabled.
 *
 * \note            This is also necessary to handle client reconnection from
 *                  the same port as described in RFC 6347 section 4.2.8 (only
 *                  the variant with cookies is supported currently). See
 *                  comments on \c mbedtls_ssl_read() for details.
 *
 * \param conf              SSL configuration
 * \param f_cookie_write    Cookie write callback
 * \param f_cookie_check    Cookie check callback
 * \param p_cookie          Context for both callbacks
 */
void mbedtls_ssl_conf_dtls_cookies( mbedtls_ssl_config *conf,
                           mbedtls_ssl_cookie_write_t *f_cookie_write,
                           mbedtls_ssl_cookie_check_t *f_cookie_check,
                           void *p_cookie );

/**
 * \brief          Set client's transport-level identification info.
 *                 (Server only. DTLS only.)
 *
 *                 This is usually the IP address (and port), but could be
 *                 anything identify the client depending on the underlying
 *                 network stack. Used for HelloVerifyRequest with DTLS.
 *                 This is *not* used to route the actual packets.
 *
 * \param ssl      SSL context
 * \param info     Transport-level info identifying the client (eg IP + port)
 * \param ilen     Length of info in bytes
 *
 * \note           An internal copy is made, so the info buffer can be reused.
 *
 * \return         0 on success,
 *                 MBEDTLS_ERR_SSL_BAD_INPUT_DATA if used on client,
 *                 MBEDTLS_ERR_SSL_ALLOC_FAILED if out of memory.
 */
int mbedtls_ssl_set_client_transport_id( mbedtls_ssl_context *ssl,
                                 const unsigned char *info,
                                 size_t ilen );

#endif /* MBEDTLS_SSL_DTLS_HELLO_VERIFY && MBEDTLS_SSL_SRV_C */

#if defined(MBEDTLS_SSL_DTLS_ANTI_REPLAY)
/**
 * \brief          Enable or disable anti-replay protection for DTLS.
 *                 (DTLS only, no effect on TLS.)
 *                 Default: enabled.
 *
 * \param conf     SSL configuration
 * \param mode     MBEDTLS_SSL_ANTI_REPLAY_ENABLED or MBEDTLS_SSL_ANTI_REPLAY_DISABLED.
 *
 * \warning        Disabling this is a security risk unless the application
 *                 protocol handles duplicated packets in a safe way. You
 *                 should not disable this without careful consideration.
 *                 However, if your application already detects duplicated
 *                 packets and needs information about them to adjust its
 *                 transmission strategy, then you'll want to disable this.
 */
void mbedtls_ssl_conf_dtls_anti_replay( mbedtls_ssl_config *conf, char mode );
#endif /* MBEDTLS_SSL_DTLS_ANTI_REPLAY */

#if defined(MBEDTLS_SSL_DTLS_BADMAC_LIMIT)
/**
 * \brief          Set a limit on the number of records with a bad MAC
 *                 before terminating the connection.
 *                 (DTLS only, no effect on TLS.)
 *                 Default: 0 (disabled).
 *
 * \param conf     SSL configuration
 * \param limit    Limit, or 0 to disable.
 *
 * \note           If the limit is N, then the connection is terminated when
 *                 the Nth non-authentic record is seen.
 *
 * \note           Records with an invalid header are not counted, only the
 *                 ones going through the authentication-decryption phase.
 *
 * \note           This is a security trade-off related to the fact that it's
 *                 often relatively easy for an active attacker ot inject UDP
 *                 datagrams. On one hand, setting a low limit here makes it
 *                 easier for such an attacker to forcibly terminated a
 *                 connection. On the other hand, a high limit or no limit
 *                 might make us waste resources checking authentication on
 *                 many bogus packets.
 */
void mbedtls_ssl_conf_dtls_badmac_limit( mbedtls_ssl_config *conf, unsigned limit );
#endif /* MBEDTLS_SSL_DTLS_BADMAC_LIMIT */

#if defined(MBEDTLS_SSL_PROTO_DTLS)

/**
 * \brief          Allow or disallow packing of multiple handshake records
 *                 within a single datagram.
 *
 * \param ssl           The SSL context to configure.
 * \param allow_packing This determines whether datagram packing may
 *                      be used or not. A value of \c 0 means that every
 *                      record will be sent in a separate datagram; a
 *                      value of \c 1 means that, if space permits,
 *                      multiple handshake messages (including CCS) belonging to
 *                      a single flight may be packed within a single datagram.
 *
 * \note           This is enabled by default and should only be disabled
 *                 for test purposes, or if datagram packing causes
 *                 interoperability issues with peers that don't support it.
 *
 * \note           Allowing datagram packing reduces the network load since
 *                 there's less overhead if multiple messages share the same
 *                 datagram. Also, it increases the handshake efficiency
 *                 since messages belonging to a single datagram will not
 *                 be reordered in transit, and so future message buffering
 *                 or flight retransmission (if no buffering is used) as
 *                 means to deal with reordering are needed less frequently.
 *
 * \note           Application records are not affected by this option and
 *                 are currently always sent in separate datagrams.
 *
 */
void mbedtls_ssl_set_datagram_packing( mbedtls_ssl_context *ssl,
                                       unsigned allow_packing );

/**
 * \brief          Set retransmit timeout values for the DTLS handshake.
 *                 (DTLS only, no effect on TLS.)
 *
 * \param conf     SSL configuration
 * \param min      Initial timeout value in milliseconds.
 *                 Default: 1000 (1 second).
 * \param max      Maximum timeout value in milliseconds.
 *                 Default: 60000 (60 seconds).
 *
 * \note           Default values are from RFC 6347 section 4.2.4.1.
 *
 * \note           The 'min' value should typically be slightly above the
 *                 expected round-trip time to your peer, plus whatever time
 *                 it takes for the peer to process the message. For example,
 *                 if your RTT is about 600ms and you peer needs up to 1s to
 *                 do the cryptographic operations in the handshake, then you
 *                 should set 'min' slightly above 1600. Lower values of 'min'
 *                 might cause spurious resends which waste network resources,
 *                 while larger value of 'min' will increase overall latency
 *                 on unreliable network links.
 *
 * \note           The more unreliable your network connection is, the larger
 *                 your max / min ratio needs to be in order to achieve
 *                 reliable handshakes.
 *
 * \note           Messages are retransmitted up to log2(ceil(max/min)) times.
 *                 For example, if min = 1s and max = 5s, the retransmit plan
 *                 goes: send ... 1s -> resend ... 2s -> resend ... 4s ->
 *                 resend ... 5s -> give up and return a timeout error.
 */
void mbedtls_ssl_conf_handshake_timeout( mbedtls_ssl_config *conf, uint32_t min, uint32_t max );
#endif /* MBEDTLS_SSL_PROTO_DTLS */

#if defined(MBEDTLS_SSL_SRV_C)
/**
 * \brief          Set the session cache callbacks (server-side only)
 *                 If not set, no session resuming is done (except if session
 *                 tickets are enabled too).
 *
 *                 The session cache has the responsibility to check for stale
 *                 entries based on timeout. See RFC 5246 for recommendations.
 *
 *                 Warning: session.peer_cert is cleared by the SSL/TLS layer on
 *                 connection shutdown, so do not cache the pointer! Either set
 *                 it to NULL or make a full copy of the certificate.
 *
 *                 The get callback is called once during the initial handshake
 *                 to enable session resuming. The get function has the
 *                 following parameters: (void *parameter, mbedtls_ssl_session *session)
 *                 If a valid entry is found, it should fill the master of
 *                 the session object with the cached values and return 0,
 *                 return 1 otherwise. Optionally peer_cert can be set as well
 *                 if it is properly present in cache entry.
 *
 *                 The set callback is called once during the initial handshake
 *                 to enable session resuming after the entire handshake has
 *                 been finished. The set function has the following parameters:
 *                 (void *parameter, const mbedtls_ssl_session *session). The function
 *                 should create a cache entry for future retrieval based on
 *                 the data in the session structure and should keep in mind
 *                 that the mbedtls_ssl_session object presented (and all its referenced
 *                 data) is cleared by the SSL/TLS layer when the connection is
 *                 terminated. It is recommended to add metadata to determine if
 *                 an entry is still valid in the future. Return 0 if
 *                 successfully cached, return 1 otherwise.
 *
 * \param conf           SSL configuration
 * \param p_cache        parmater (context) for both callbacks
 * \param f_get_cache    session get callback
 * \param f_set_cache    session set callback
 */
void mbedtls_ssl_conf_session_cache( mbedtls_ssl_config *conf,
        void *p_cache,
        int (*f_get_cache)(void *, mbedtls_ssl_session *),
        int (*f_set_cache)(void *, const mbedtls_ssl_session *) );
#endif /* MBEDTLS_SSL_SRV_C */

#if defined(MBEDTLS_SSL_CLI_C)
/**
 * \brief          Request resumption of session (client-side only)
 *                 Session data is copied from presented session structure.
 *
 * \param ssl      SSL context
 * \param session  session context
 *
 * \return         0 if successful,
 *                 MBEDTLS_ERR_SSL_ALLOC_FAILED if memory allocation failed,
 *                 MBEDTLS_ERR_SSL_BAD_INPUT_DATA if used server-side or
 *                 arguments are otherwise invalid
 *
 * \sa             mbedtls_ssl_get_session()
 */
int mbedtls_ssl_set_session( mbedtls_ssl_context *ssl, const mbedtls_ssl_session *session );
#endif /* MBEDTLS_SSL_CLI_C */

/**
 * \brief          Load serialized session data into a session structure.
 *                 On client, this can be used for loading saved sessions
 *                 before resuming them with mbedstls_ssl_set_session().
 *                 On server, this can be used for alternative implementations
 *                 of session cache or session tickets.
 *
 * \warning        If a peer certificate chain is associated with the session,
 *                 the serialized state will only contain the peer's
 *                 end-entity certificate and the result of the chain
 *                 verification (unless verification was disabled), but not
 *                 the rest of the chain.
 *
 * \see            mbedtls_ssl_session_save()
 * \see            mbedtls_ssl_set_session()
 *
 * \param session  The session structure to be populated. It must have been
 *                 initialised with mbedtls_ssl_session_init() but not
 *                 populated yet.
 * \param buf      The buffer holding the serialized session data. It must be a
 *                 readable buffer of at least \p len bytes.
 * \param len      The size of the serialized data in bytes.
 *
 * \return         \c 0 if successful.
 * \return         #MBEDTLS_ERR_SSL_ALLOC_FAILED if memory allocation failed.
 * \return         #MBEDTLS_ERR_SSL_BAD_INPUT_DATA if input data is invalid.
 * \return         #MBEDTLS_ERR_SSL_VERSION_MISMATCH if the serialized data
 *                 was generated in a different version or configuration of
 *                 Mbed TLS.
 * \return         Another negative value for other kinds of errors (for
 *                 example, unsupported features in the embedded certificate).
 */
int mbedtls_ssl_session_load( mbedtls_ssl_session *session,
                              const unsigned char *buf,
                              size_t len );

/**
 * \brief          Save session structure as serialized data in a buffer.
 *                 On client, this can be used for saving session data,
 *                 potentially in non-volatile storage, for resuming later.
 *                 On server, this can be used for alternative implementations
 *                 of session cache or session tickets.
 *
 * \see            mbedtls_ssl_session_load()
 * \see            mbedtls_ssl_get_session_pointer()
 *
 * \param session  The session structure to be saved.
 * \param buf      The buffer to write the serialized data to. It must be a
 *                 writeable buffer of at least \p len bytes, or may be \c
 *                 NULL if \p len is \c 0.
 * \param buf_len  The number of bytes available for writing in \p buf.
 * \param olen     The size in bytes of the data that has been or would have
 *                 been written. It must point to a valid \c size_t.
 *
 * \note           \p olen is updated to the correct value regardless of
 *                 whether \p buf_len was large enough. This makes it possible
 *                 to determine the necessary size by calling this function
 *                 with \p buf set to \c NULL and \p buf_len to \c 0.
 *
 * \return         \c 0 if successful.
 * \return         #MBEDTLS_ERR_SSL_BUFFER_TOO_SMALL if \p buf is too small.
 */
int mbedtls_ssl_session_save( const mbedtls_ssl_session *session,
                              unsigned char *buf,
                              size_t buf_len,
                              size_t *olen );

/**
 * \brief          Get a pointer to the current session structure, for example
 *                 to serialize it.
 *
 * \warning        Ownership of the session remains with the SSL context, and
 *                 the returned pointer is only guaranteed to be valid until
 *                 the next API call operating on the same \p ssl context.
 *
 * \see            mbedtls_ssl_session_save()
 *
 * \param ssl      The SSL context.
 *
 * \return         A pointer to the current session if successful.
 * \return         \c NULL if no session is active.
 */
const mbedtls_ssl_session *mbedtls_ssl_get_session_pointer( const mbedtls_ssl_context *ssl );

/**
 * \brief               Set the list of allowed ciphersuites and the preference
 *                      order. First in the list has the highest preference.
 *                      (Overrides all version-specific lists)
 *
 *                      The ciphersuites array is not copied, and must remain
 *                      valid for the lifetime of the ssl_config.
 *
 *                      Note: The server uses its own preferences
 *                      over the preference of the client unless
 *                      MBEDTLS_SSL_SRV_RESPECT_CLIENT_PREFERENCE is defined!
 *
 * \param conf          SSL configuration
 * \param ciphersuites  0-terminated list of allowed ciphersuites
 */
void mbedtls_ssl_conf_ciphersuites( mbedtls_ssl_config *conf,
                                   const int *ciphersuites );
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
