5Breeze/WKnob/APP/BTHome/BTHome.c

/*
 * BTHome.c
 *
 *  Created on: 2024骞�10鏈�27鏃�
 *      Author: LQY
 */

#include "CH59x_common.h"
#include "BTHome.h"

void set_uint24(uint24* data,uint32 value){
    if (data == NULL || value > 0xFFFFFF) {
        return;
    }
    data->data[0] = value & 0xFF;
    data->data[1] = (value >> 8) & 0xFF;
    data->data[2] = (value >> 16) & 0xFF;
}

#ifdef BTHOME_ENABLE_ENCRYPT
#include "mbedtls/include/mbedtls/ccm.h"
#include "stdlib.h"
mbedtls_ccm_context m_encryptCTX;

void convert_hex_string_to_bytes(const char *hex_string, uint8_t *output_array, size_t output_len) {
  for (size_t i = 0; i < output_len; i++) {

    char hex_str[3] = { hex_string[i * 2], hex_string[i * 2 + 1], '\0' };
    output_array[i] = (uint8_t)strtol(hex_str, NULL, 16);
  }
}

int bthome_encrypt_init()
{
    uint8_t hex_bthome_aes_key[16];
    convert_hex_string_to_bytes(bthome_aes_key, hex_bthome_aes_key , 16 );
    mbedtls_ccm_init(&m_encryptCTX);
	  return mbedtls_ccm_setkey( &m_encryptCTX, MBEDTLS_CIPHER_ID_AES, hex_bthome_aes_key, sizeof(hex_bthome_aes_key) * 8);
}

void bthome_get_nonce(const uint8 mac[6], bthome_server_data_type server , uint8 nonce[13]){
	memcpy(nonce,mac,6);
	memcpy(nonce+6,&server.UUID_16Bit,2);
	memcpy(nonce+8,&server.device_information,1);
	memcpy(nonce+9,&server.counter,4);
}
/// @brief 鍔犲瘑鏁版嵁


/// @param server_in 	杈撳叆鐨刡thome鏈嶅姟鏁版嵁
/// @param server_out 	杈撳嚭鐨刡thome鏈嶅姟鏁版嵁
/// @return 
int bthome_encryption(const uint8 mac[6] , mbedtls_ccm_context *ctx , bthome_server_data_type server_in, bthome_server_data_type *server_out )
{
    uint8 nonce[13] ;
    bthome_get_nonce( mac, server_in ,nonce);
    // 鍔犲瘑
    return mbedtls_ccm_encrypt_and_tag( ctx, sizeof(BTHomeV2_sensor_type) , nonce, sizeof(nonce), 0, 0,
                                        (uint8_t *)&server_in.sensor, (uint8_t *)&server_out->sensor, (uint8_t *)&server_out->mic,
                                          sizeof(server_out->mic));
}

int bthome_sensor_update( const uint8 *mac, BTHomeV2_sensor_type sensor ,  BTHome_advertData_type *advertData ){
  memcpy(&advertData->server.sensor,&sensor,sizeof(BTHomeV2_sensor_type));
	advertData->server.counter ++ ;
  //浣跨敤绉橀挜 m_encryptCTX 鍔犲瘑鏁版嵁
  return bthome_encryption( mac , &m_encryptCTX, advertData->server, &advertData->server ); 

}
#else

int bthome_sensor_update( const uint8 *mac, BTHomeV2_sensor_type sensor ,  BTHome_advertData_type *advertData ){
    memcpy(&advertData->server.sensor,&sensor,sizeof(BTHomeV2_sensor_type)) ;
    return 0 ;
}
int bthome_encrypt_init(){
    return 0 ;
}

#endif
